Commander-bao/BlueberryPi/2.Docs/Allwinner H6/硬件资料/9、原型机设计资料/H6_PRO_DDR3_V1_1.pdf

D | D
C | C
B | B
A | A
Schematics Index： | HJ
Revision | Description | Date | Drawn | Checked

# P01: REVISION HISTORY P02: BLOCK P03: POWER TREE P04: GPIO ASSIGNMENT P05: SOC1 P06: SOC2 P07: DDR3 16X2 P08: POWER P09: NAND-eMMC P10: CARD-USB-IR-SPDIF P11: KEY-LED-ETH-DEBUG P12: AV-HDMI P13: WIFI-BT 2T2R P14: WIFI-BT 1T1R

Ver 0.5 | Initial Version | 2016-12-26

# REVISION HISTORY

Ver 0.9 | 2017-04-10 | HJ
Ver 1.0 | 2017-06-14 | HJ

Design Name

Size A3 | Page Name REVISION HISTORY REVISION HISTORY REVISION HISTORY | Rev
Date: Thursday, June 22, 2017 Thursday, June 22, 2017 Thursday, June 22, 2017 | Sheet 1 1 1 of 14 14 14

# AllWinner Technology Co.,Ltd

## H6-PROTO

Design Name

# AllWinner Technology Co.,Ltd

Design Name

# AllWinner Technology Co.,Ltd

# confidential

D | D

# BLOCK

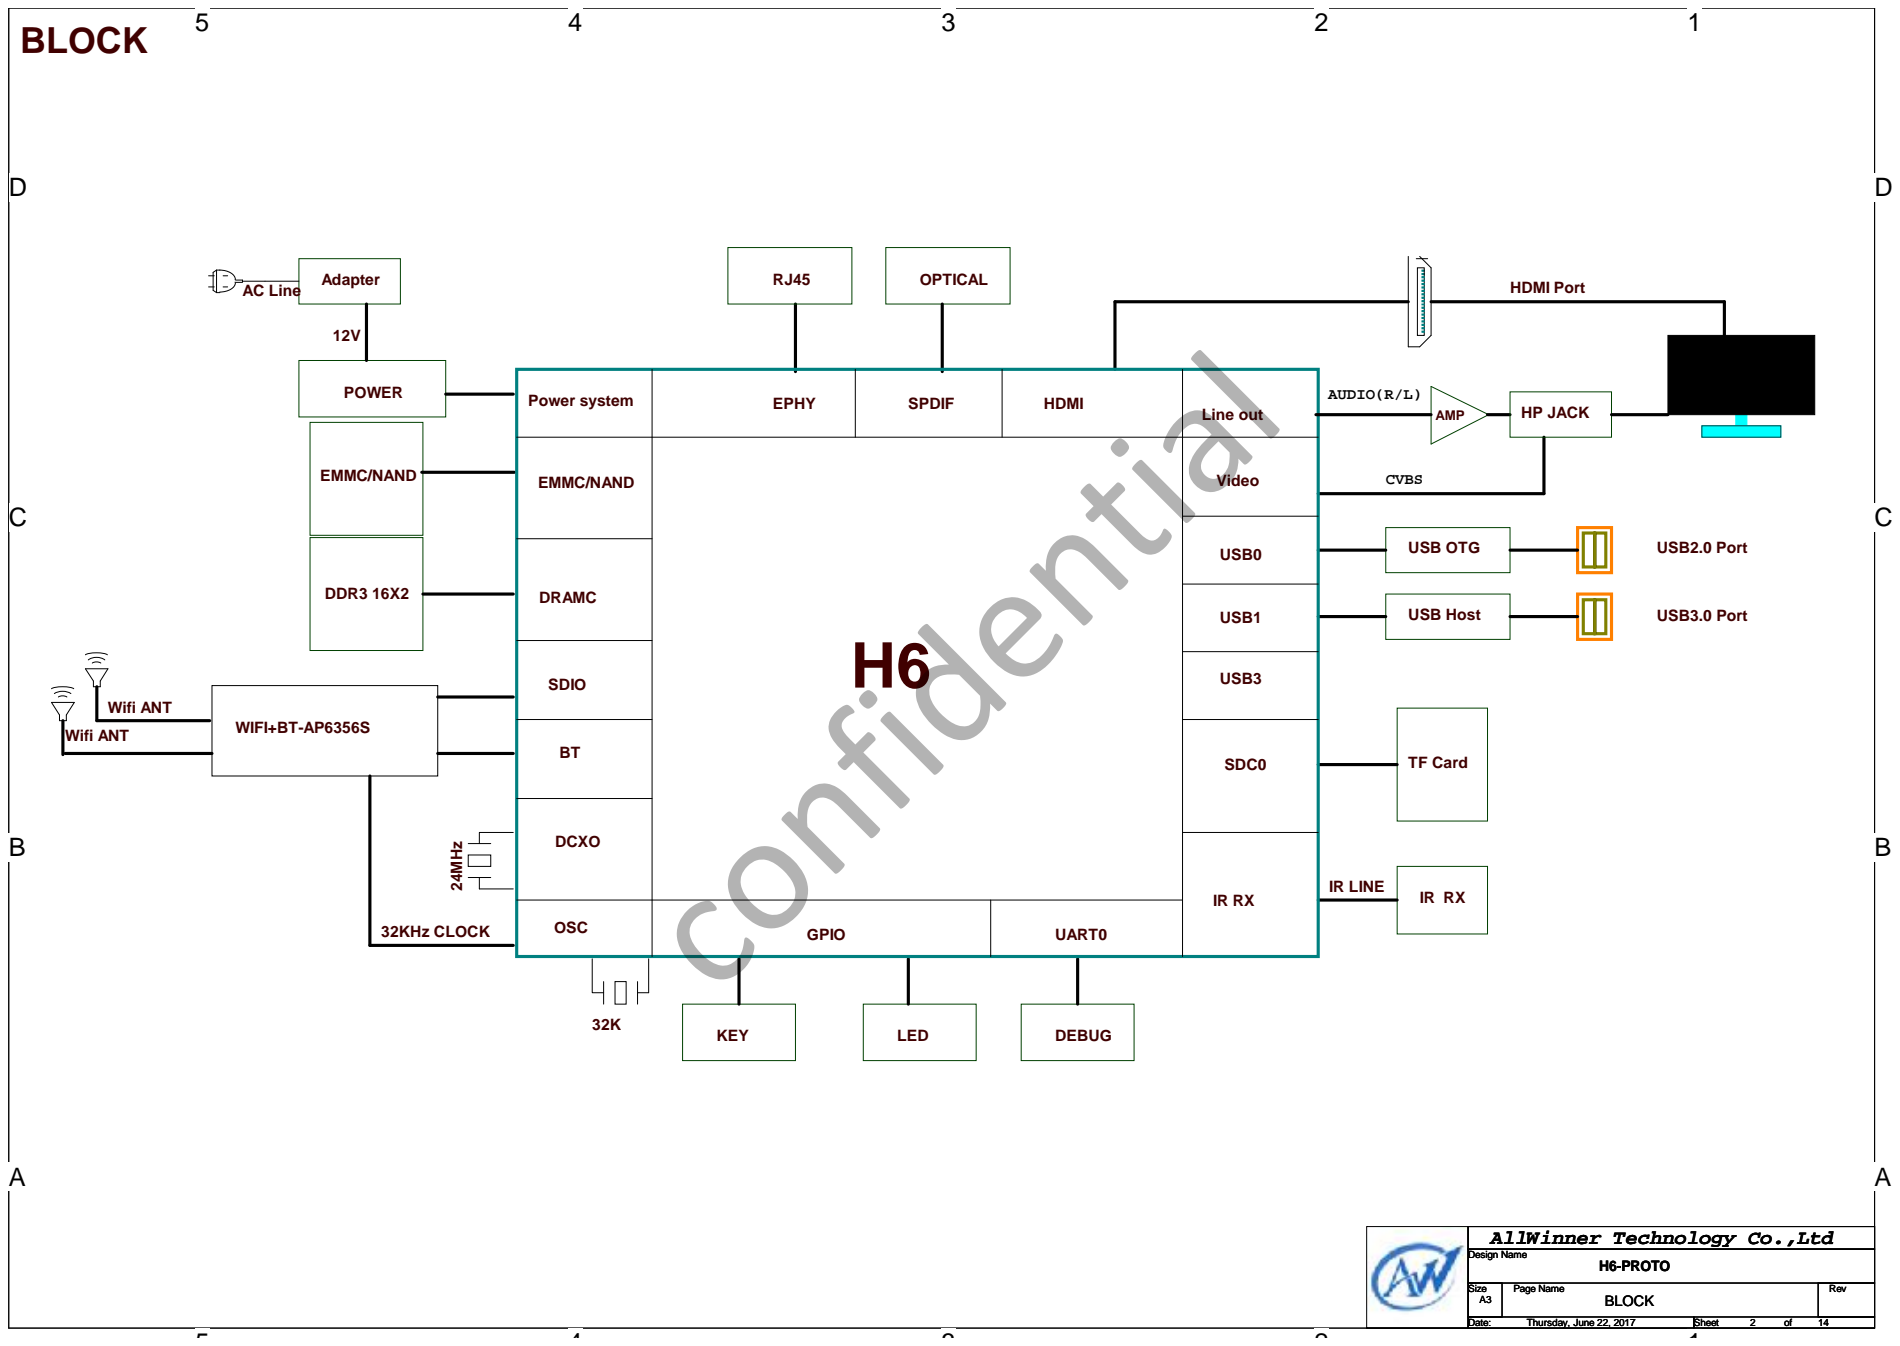
[picture p25: page 2]
UART0; KEY; DEBUG; GPIO; Power system; EMMC/NAND; EPHY; SPDIF; HDMI; OSC; USB1; USB2.0 Port; USB3.0 Port; USB OTG; WIFI+BT-AP6356S; Wifi ANT; LED; SDC0; TF Card; IR LINE; USB0; Video; Line out; AUDIO(R/L); AMP; CVBS; HP JACK; HDMI Port Adapter; OPTICAL; POWER; AC Line; DRAMC; DDR3 16X2; SDIO; USB3; USB Host; DCXO; 24MHz; 32KHz CLOCK; Design Name; BLOCK; Thursday, June 22, 2017; confidential

AllWinner Technology Co.,Ltd

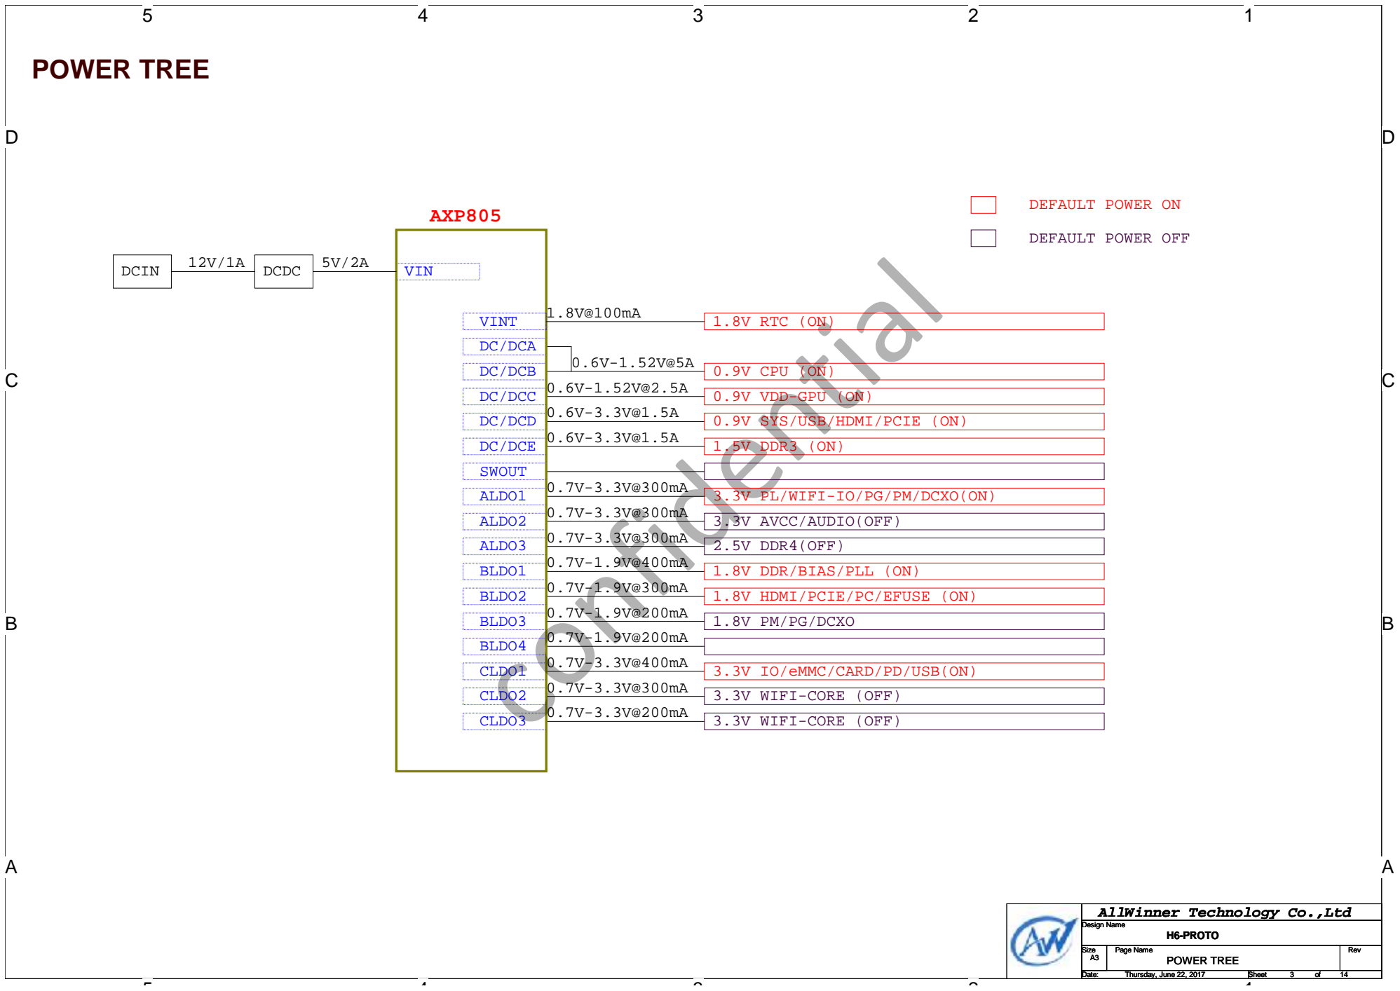
[picture p26: figure]
POWER TREE; 3.3V WIFI-CORE (OFF); 0.9V VDD-GPU (ON) 0.6V-1.52V@2.5A; DC/DCA DC/DCB; VIN; DC/DCC; 0.9V CPU (ON); DC/DCD 1.5V DDR3 (ON) 0.6V-3.3V@1.5A DC/DCE; SWOUT; ALDO1; 3.3V PL/WIFI-IO/PG/PM/DCXO(ON); ALDO2; ALDO3; 1.8V DDR/BIAS/PLL (ON); BLDO2 0.7V-1.9V@200mA BLDO3; CLDO1; BLDO4; CLDO2 CLDO3; AXP805; 2.5V DDR4(OFF); 1.8V PM/PG/DCXO; 3.3V AVCC/AUDIO(OFF); 1.8V HDMI/PCIE/PC/EFUSE (ON); 3.3V IO/eMMC/CARD/PD/USB(ON); BLDO1; DCIN; 0.9V SYS/USB/HDMI/PCIE (ON); VINT; 1.8V RTC (ON) 1.8V@100mA; DEFAULT POWER ON; DEFAULT POWER OFF; DCDC; Design Name; AllWinner Technology Co.,Ltd; POWER TREE POWER TREE POWER TREE; confidential

Thursday, June 22, 2017 Thursday, June 22, 2017 Thursday, June 22, 2017 | 3 3 3 14 14 14

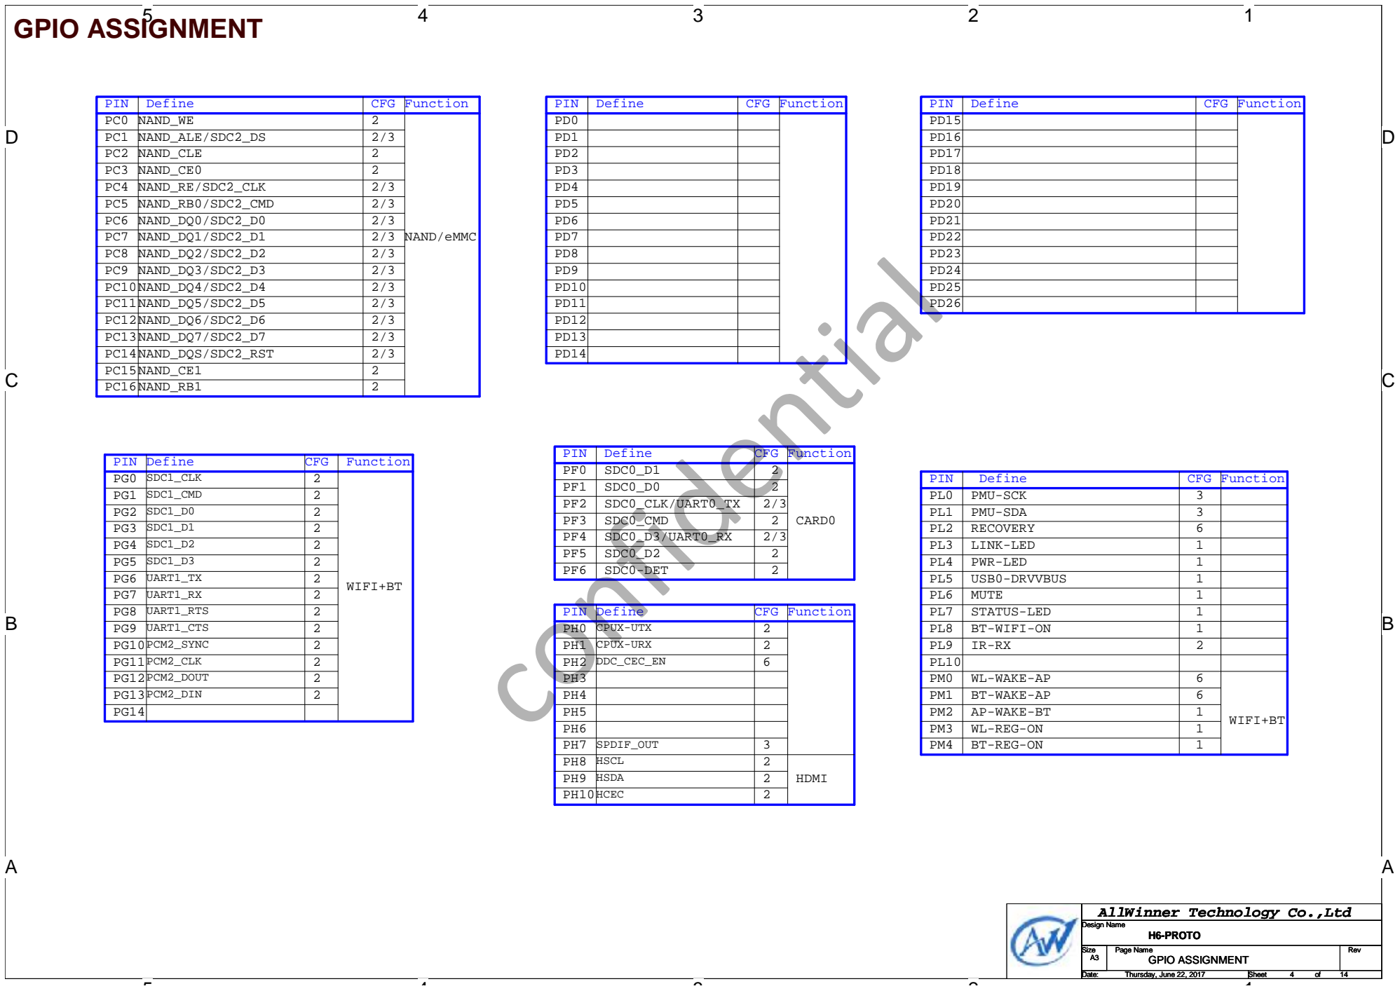
[picture p27: figure]
GPIO ASSIGNMENT; SDC0_D2; SDC0_CMD; SDC0_CLK/UART0_TX; SDC0_D1 SDC0_D0; SDC0_D3/UART0_RX; CARD0 SDC1_D1; SDC1_D0; SDC1_CMD; SDC1_CLK; UART1_RTS; UART1_RX; UART1_TX; SDC1_D3; SDC1_D2; SDC0-DET; PIN; Define; CFG; Function; NAND_DQ4/SDC2_D4; NAND_DQ3/SDC2_D3; NAND_DQ7/SDC2_D7; NAND_DQ6/SDC2_D6; NAND_DQ5/SDC2_D5; NAND_CE1; NAND_DQS/SDC2_RST; NAND_DQ1/SDC2_D1 NAND_DQ2/SDC2_D2; NAND_DQ0/SDC2_D0; NAND_RB0/SDC2_CMD; NAND_ALE/SDC2_DS NAND_CLE; NAND_WE; NAND_CE0 NAND_RE/SDC2_CLK; NAND_RB1; NAND/eMMC; PCM2_DIN; PCM2_DOUT; PCM2_CLK; PCM2_SYNC; UART1_CTS; SPDIF_OUT; HCEC; HSDA; PMU-SCK; PWR-LED; LINK-LED; RECOVERY; PMU-SDA; STATUS-LED; MUTE; WL-REG-ON; AP-WAKE-BT; BT-WAKE-AP; WL-WAKE-AP; BT-REG-ON; CPUX-UTX CPUX-URX; WIFI+BT; USB0-DRVVBUS; BT-WIFI-ON; DDC_CEC_EN; Thursday, June 22, 2017; confidential

PH8 | HSCL | 2 | HDMI | AllWinner Technology Co.,Ltd AllWinner Technology Co.,Ltd AllWinner Technology Co.,Ltd Design Name Design Name Design Name GPIO ASSIGNMENT GPIO ASSIGNMENT GPIO ASSIGNMENT

D | D

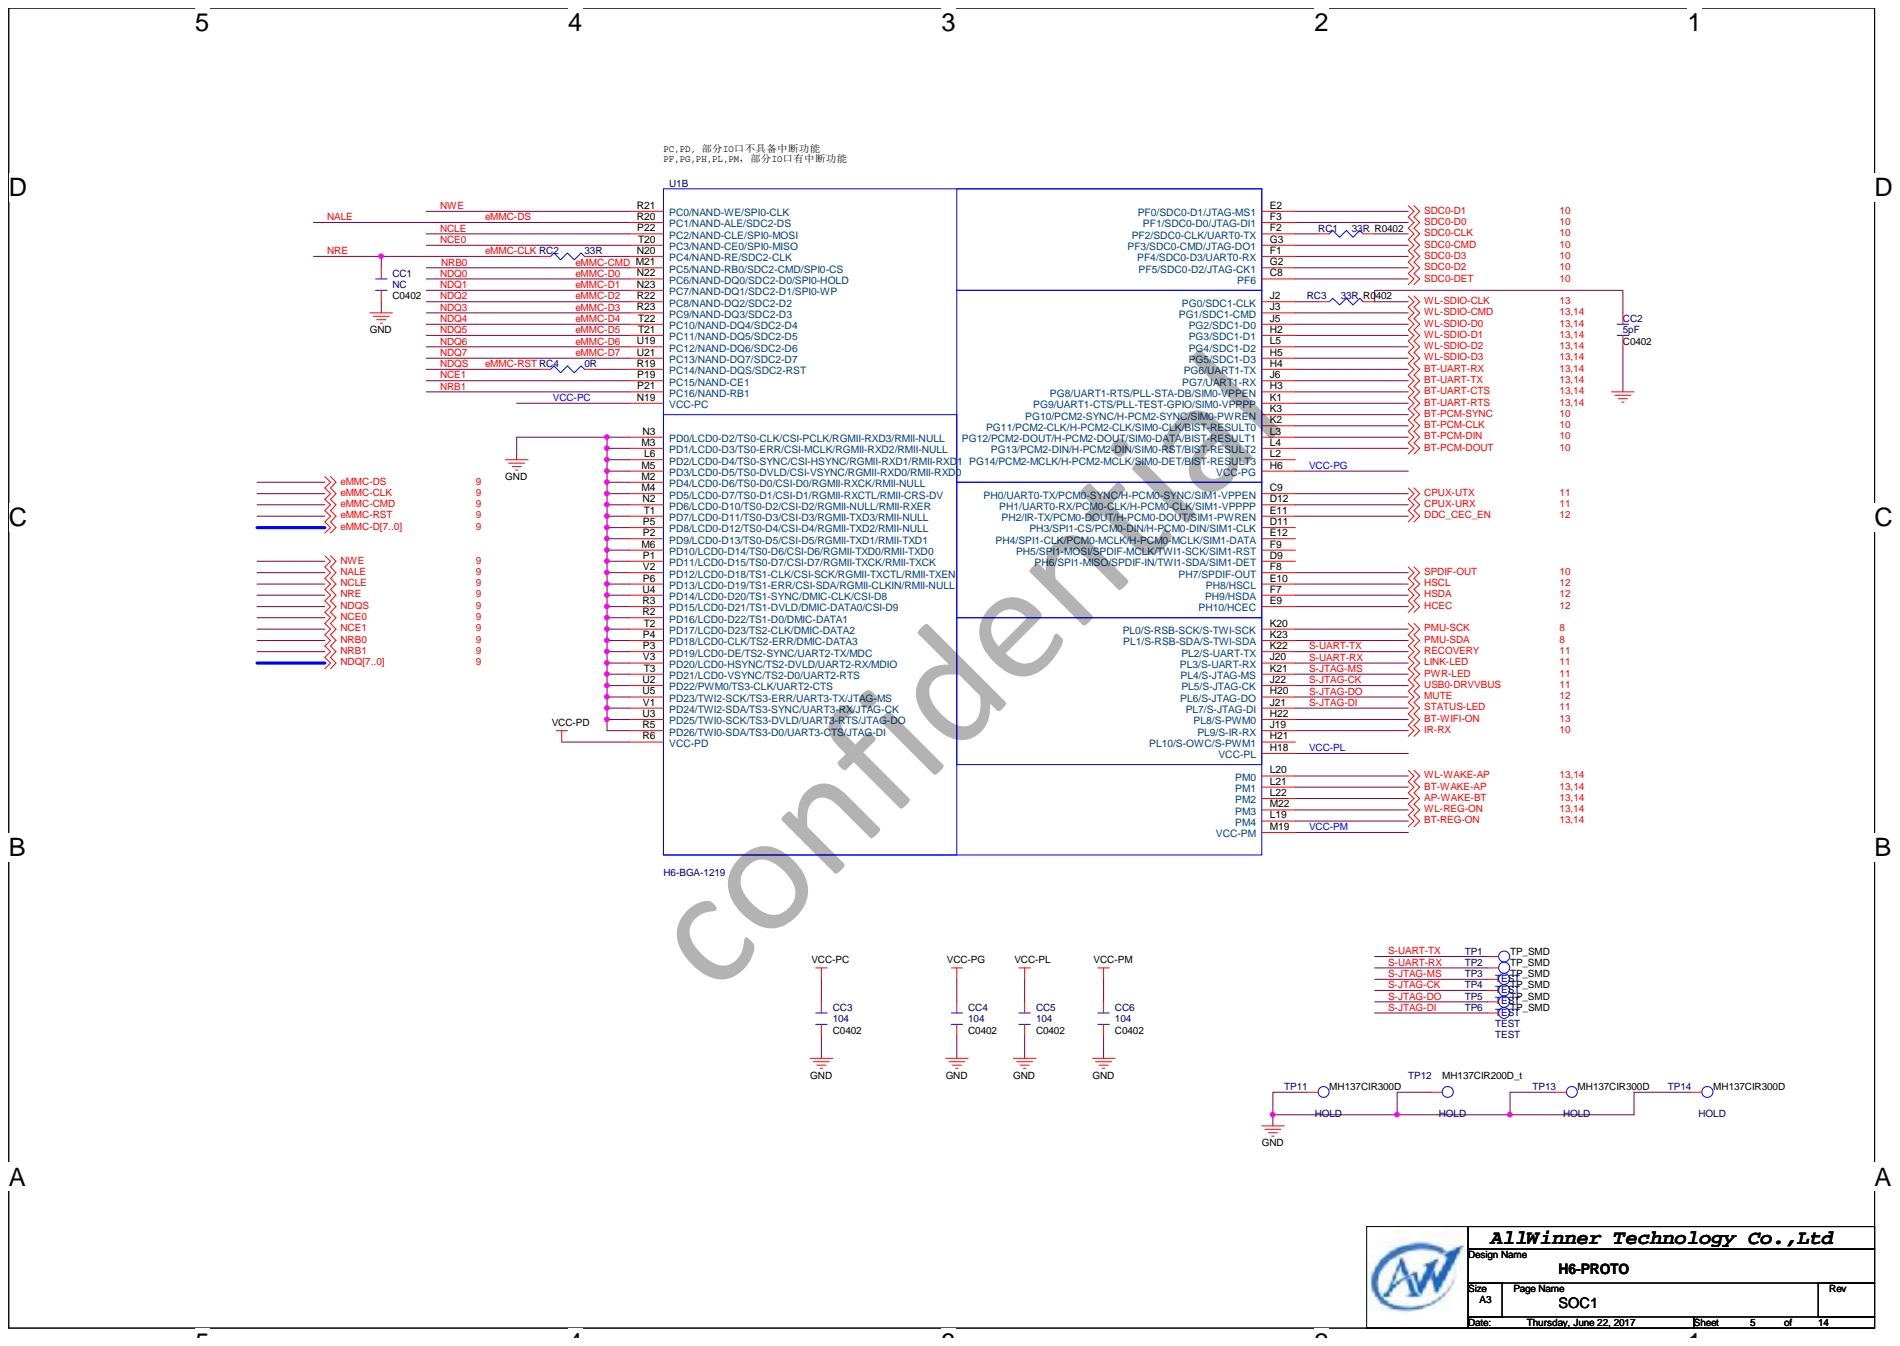
[picture p28: page 5]

PC,PD, 部分IO口不具备中断功能
PF,PG,PH,PL,PM，部分IO口有中断功能

PG8/UART1-RTS/PLL-STA-DB/SIM0-VPPEN
PG9/UART1-CTS/PLL-TEST-GPIO/SIM0-VPPPP
PG10/PCM2-SYNC/H-PCM2-SYNC/SIM0-PWREN

PD0/LCD0-D2/TS0-CLK/CSI-PCLK/RGMII-RXD3/RMII-NULL
PD1/LCD0-D3/TS0-ERR/CSI-MCLK/RGMII-RXD2/RMII-NULL
PD2/LCD0-D4/TS0-SYNC/CSI-HSYNC/RGMII-RXD1/RMII-RXD1
PD3/LCD0-D5/TS0-DVLD/CSI-VSYNC/RGMII-RXD0/RMII-RXD0
PD4/LCD0-D6/TS0-D0/CSI-D0/RGMII-RXCK/RMII-NULL
PD5/LCD0-D7/TS0-D1/CSI-D1/RGMII-RXCTL/RMII-CRS-DV M4
PD6/LCD0-D10/TS0-D2/CSI-D2/RGMII-NULL/RMII-RXER
PD7/LCD0-D11/TS0-D3/CSI-D3/RGMII-TXD3/RMII-NULL
PD8/LCD0-D12/TS0-D4/CSI-D4/RGMII-TXD2/RMII-NULL
PD9/LCD0-D13/TS0-D5/CSI-D5/RGMII-TXD1/RMII-TXD1
PD10/LCD0-D14/TS0-D6/CSI-D6/RGMII-TXD0/RMII-TXD0
PD11/LCD0-D15/TS0-D7/CSI-D7/RGMII-TXCK/RMII-TXCK P1
PD12/LCD0-D18/TS1-CLK/CSI-SCK/RGMII-TXCTL/RMII-TXEN
PD13/LCD0-D19/TS1-ERR/CSI-SDA/RGMII-CLKIN/RMII-NULL
PD14/LCD0-D20/TS1-SYNC/DMIC-CLK/CSI-D8
PD15/LCD0-D21/TS1-DVLD/DMIC-DATA0/CSI-D9
PD16/LCD0-D22/TS1-D0/DMIC-DATA1
PD17/LCD0-D23/TS2-CLK/DMIC-DATA2
PD18/LCD0-CLK/TS2-ERR/DMIC-DATA3
PD19/LCD0-DE/TS2-SYNC/UART2-TX/MDC P3
PD20/LCD0-HSYNC/TS2-DVLD/UART2-RX/MDIO V3
PD21/LCD0-VSYNC/TS2-D0/UART2-RTS T3
PD22/PWM0/TS3-CLK/UART2-CTS U2
PD23/TWI2-SCK/TS3-ERR/UART3-TX/JTAG-MS U5
PD24/TWI2-SDA/TS3-SYNC/UART3-RX/JTAG-CK V1
PD25/TWI0-SCK/TS3-DVLD/UART3-RTS/JTAG-DO U3
PD26/TWI0-SDA/TS3-D0/UART3-CTS/JTAG-DI R5
VCC-PD R6

PG11/PCM2-CLK/H-PCM2-CLK/SIM0-CLK/BIST-RESULT0
PG12/PCM2-DOUT/H-PCM2-DOUT/SIM0-DATA/BIST-RESULT1
PG13/PCM2-DIN/H-PCM2-DIN/SIM0-RST/BIST-RESULT2
PG14/PCM2-MCLK/H-PCM2-MCLK/SIM0-DET/BIST-RESULT3

PH0/UART0-TX/PCM0-SYNC/H-PCM0-SYNC/SIM1-VPPEN
PH1/UART0-RX/PCM0-CLK/H-PCM0-CLK/SIM1-VPPPP
PH2/IR-TX/PCM0-DOUT/H-PCM0-DOUT/SIM1-PWREN
PH3/SPI1-CS/PCM0-DIN/H-PCM0-DIN/SIM1-CLK D11
PH4/SPI1-CLK/PCM0-MCLK/H-PCM0-MCLK/SIM1-DATA
PH5/SPI1-MOSI/SPDIF-MCLK/TWI1-SCK/SIM1-RST F9
PH6/SPI1-MISO/SPDIF-IN/TWI1-SDA/SIM1-DET

PL0/S-RSB-SCK/S-TWI-SCK K20
PL1/S-RSB-SDA/S-TWI-SDA K23

AllWinner Technology Co.,Ltd

D | D

## TEST

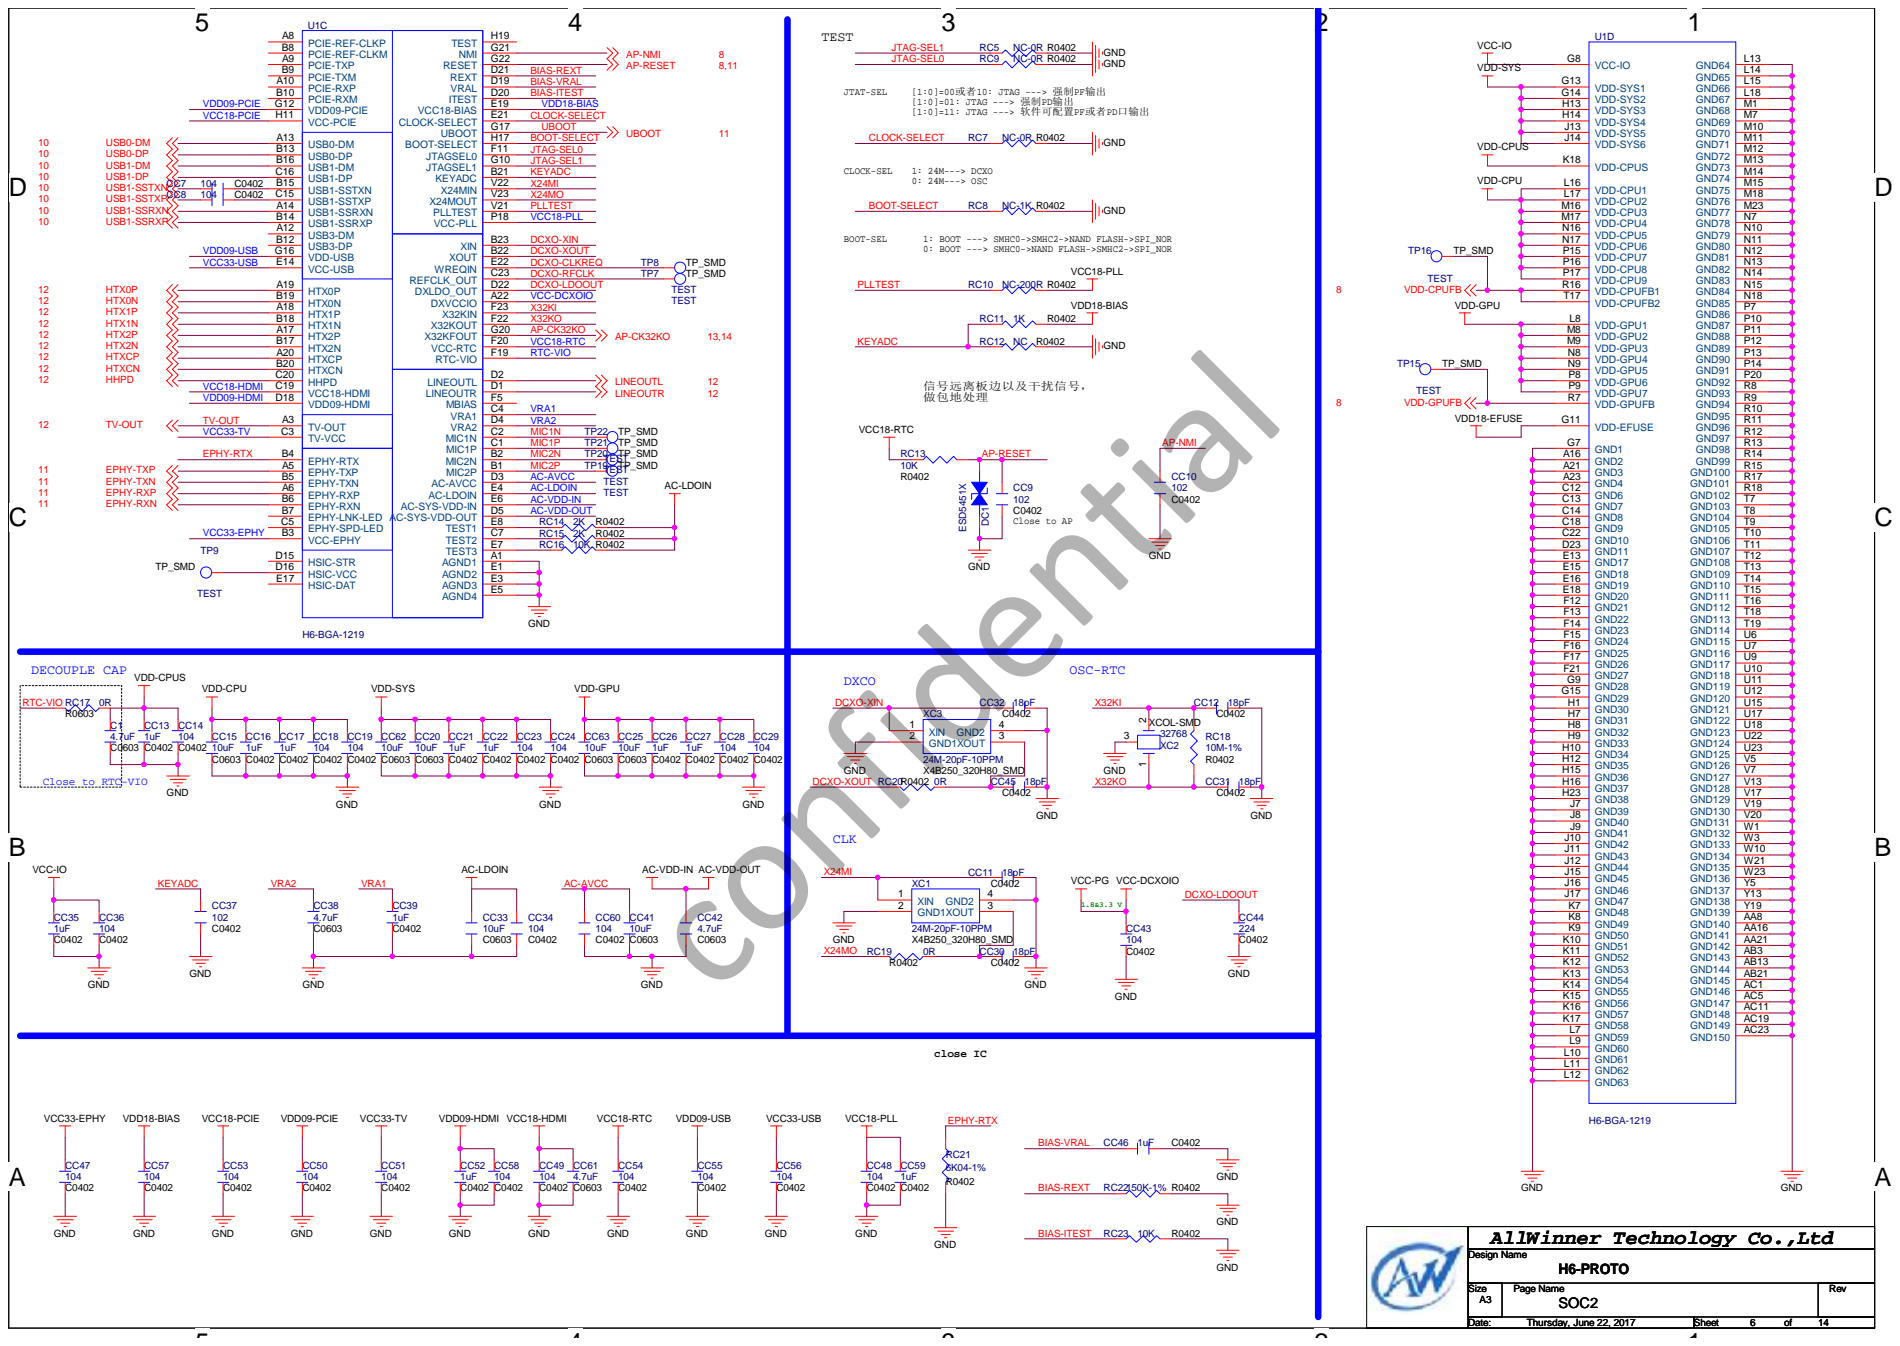
[picture p29: page 6]

VCC-EPHY B3
E17 HSIC-VCC D16 HSIC-STR

Close to RTC-VIO

VCC-PG VCC-DCXOIO

AllWinner Technology Co.,Ltd

D

D

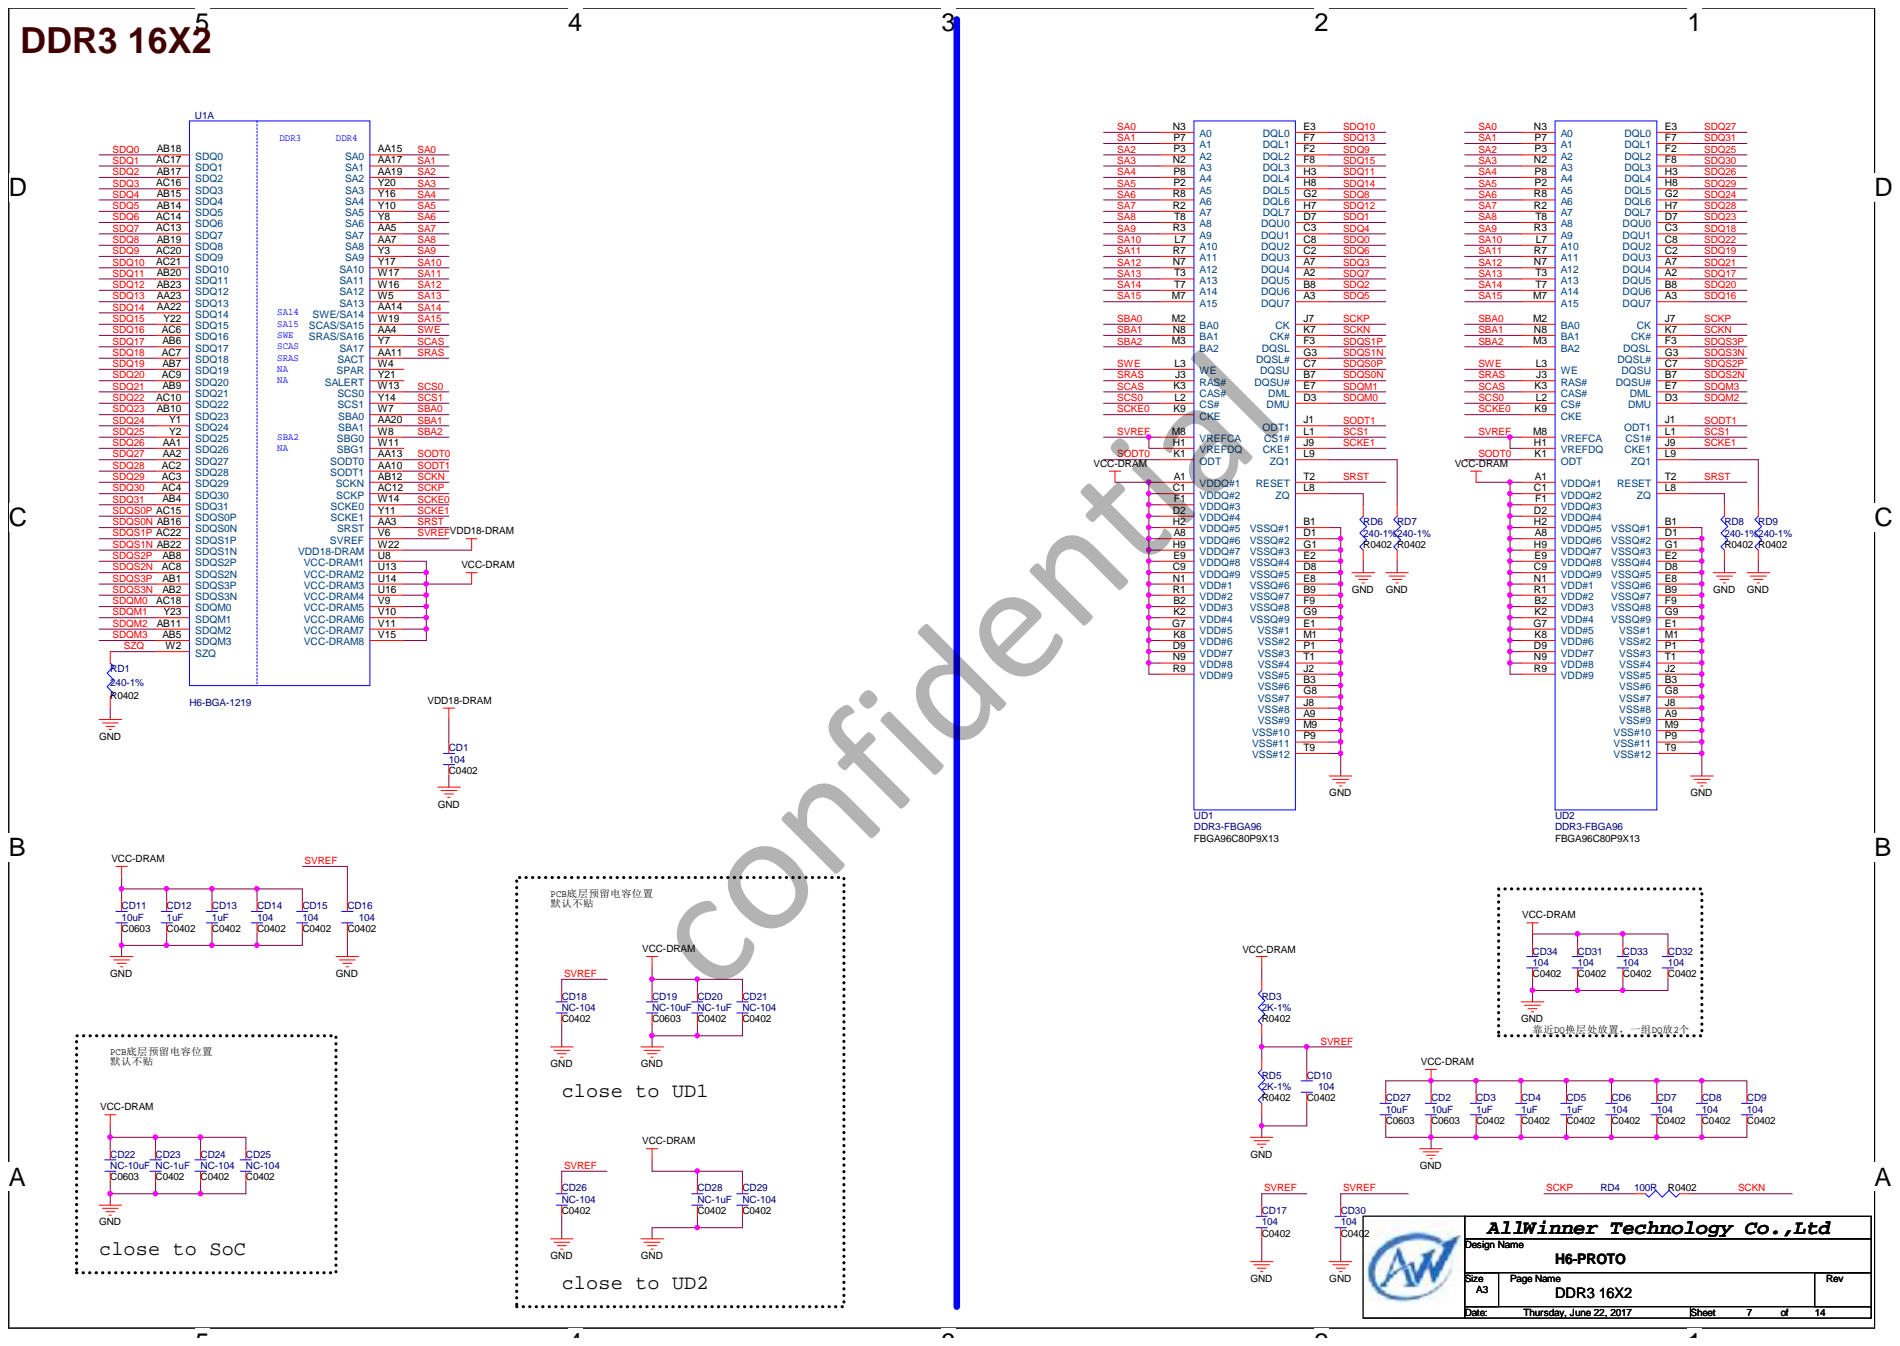
[picture p30: page 7]

SCKP
AllWinner Technology Co.,Ltd

# DCIN

12V->5V

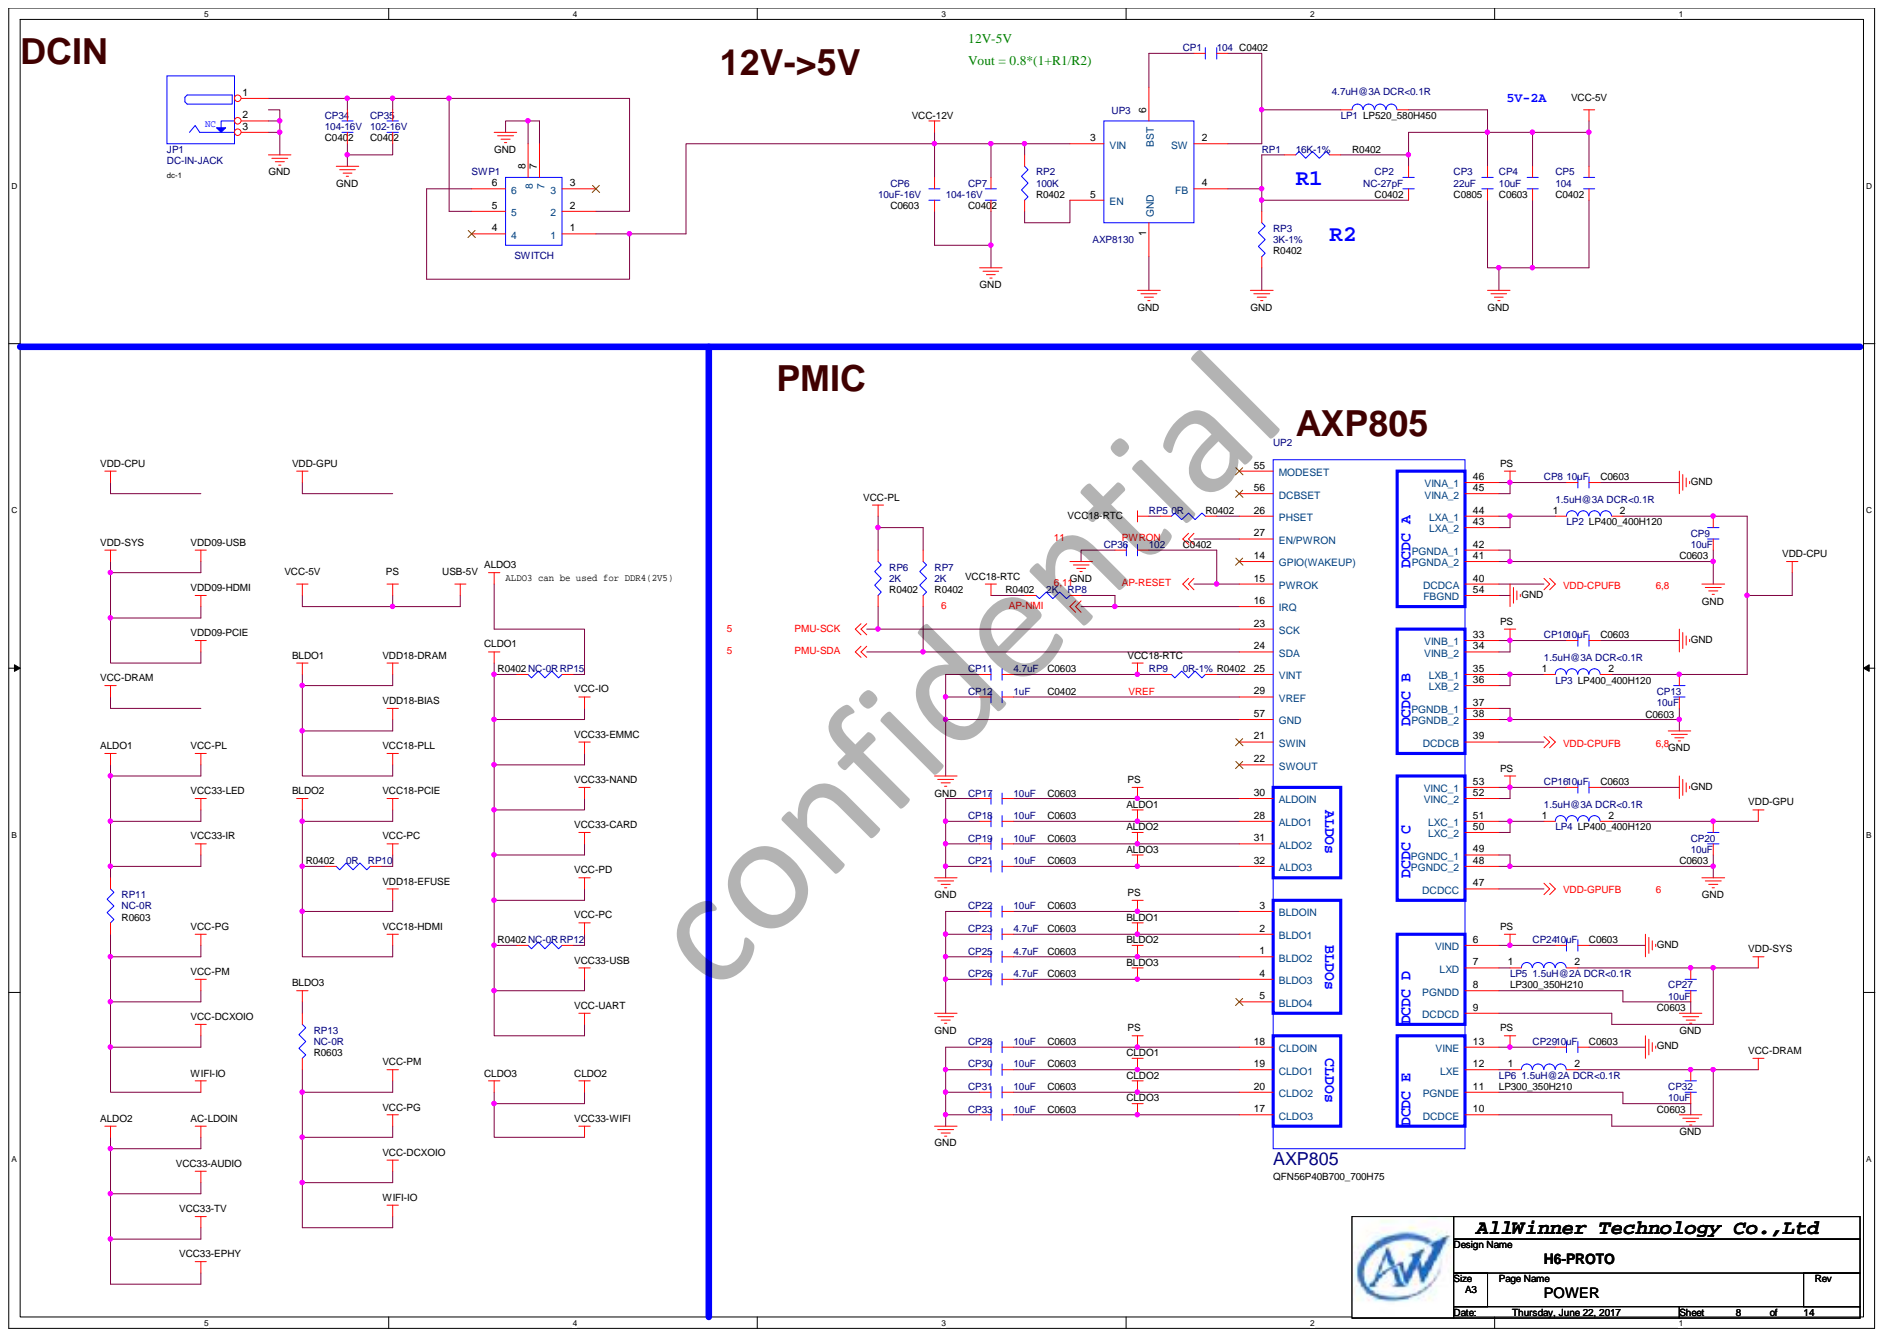
[picture p31: page 8]

ALDO3
ALDO3 can be used for DDR4(2V5)

AllWinner Technology Co.,Ltd

D | D

# NAND eMMC

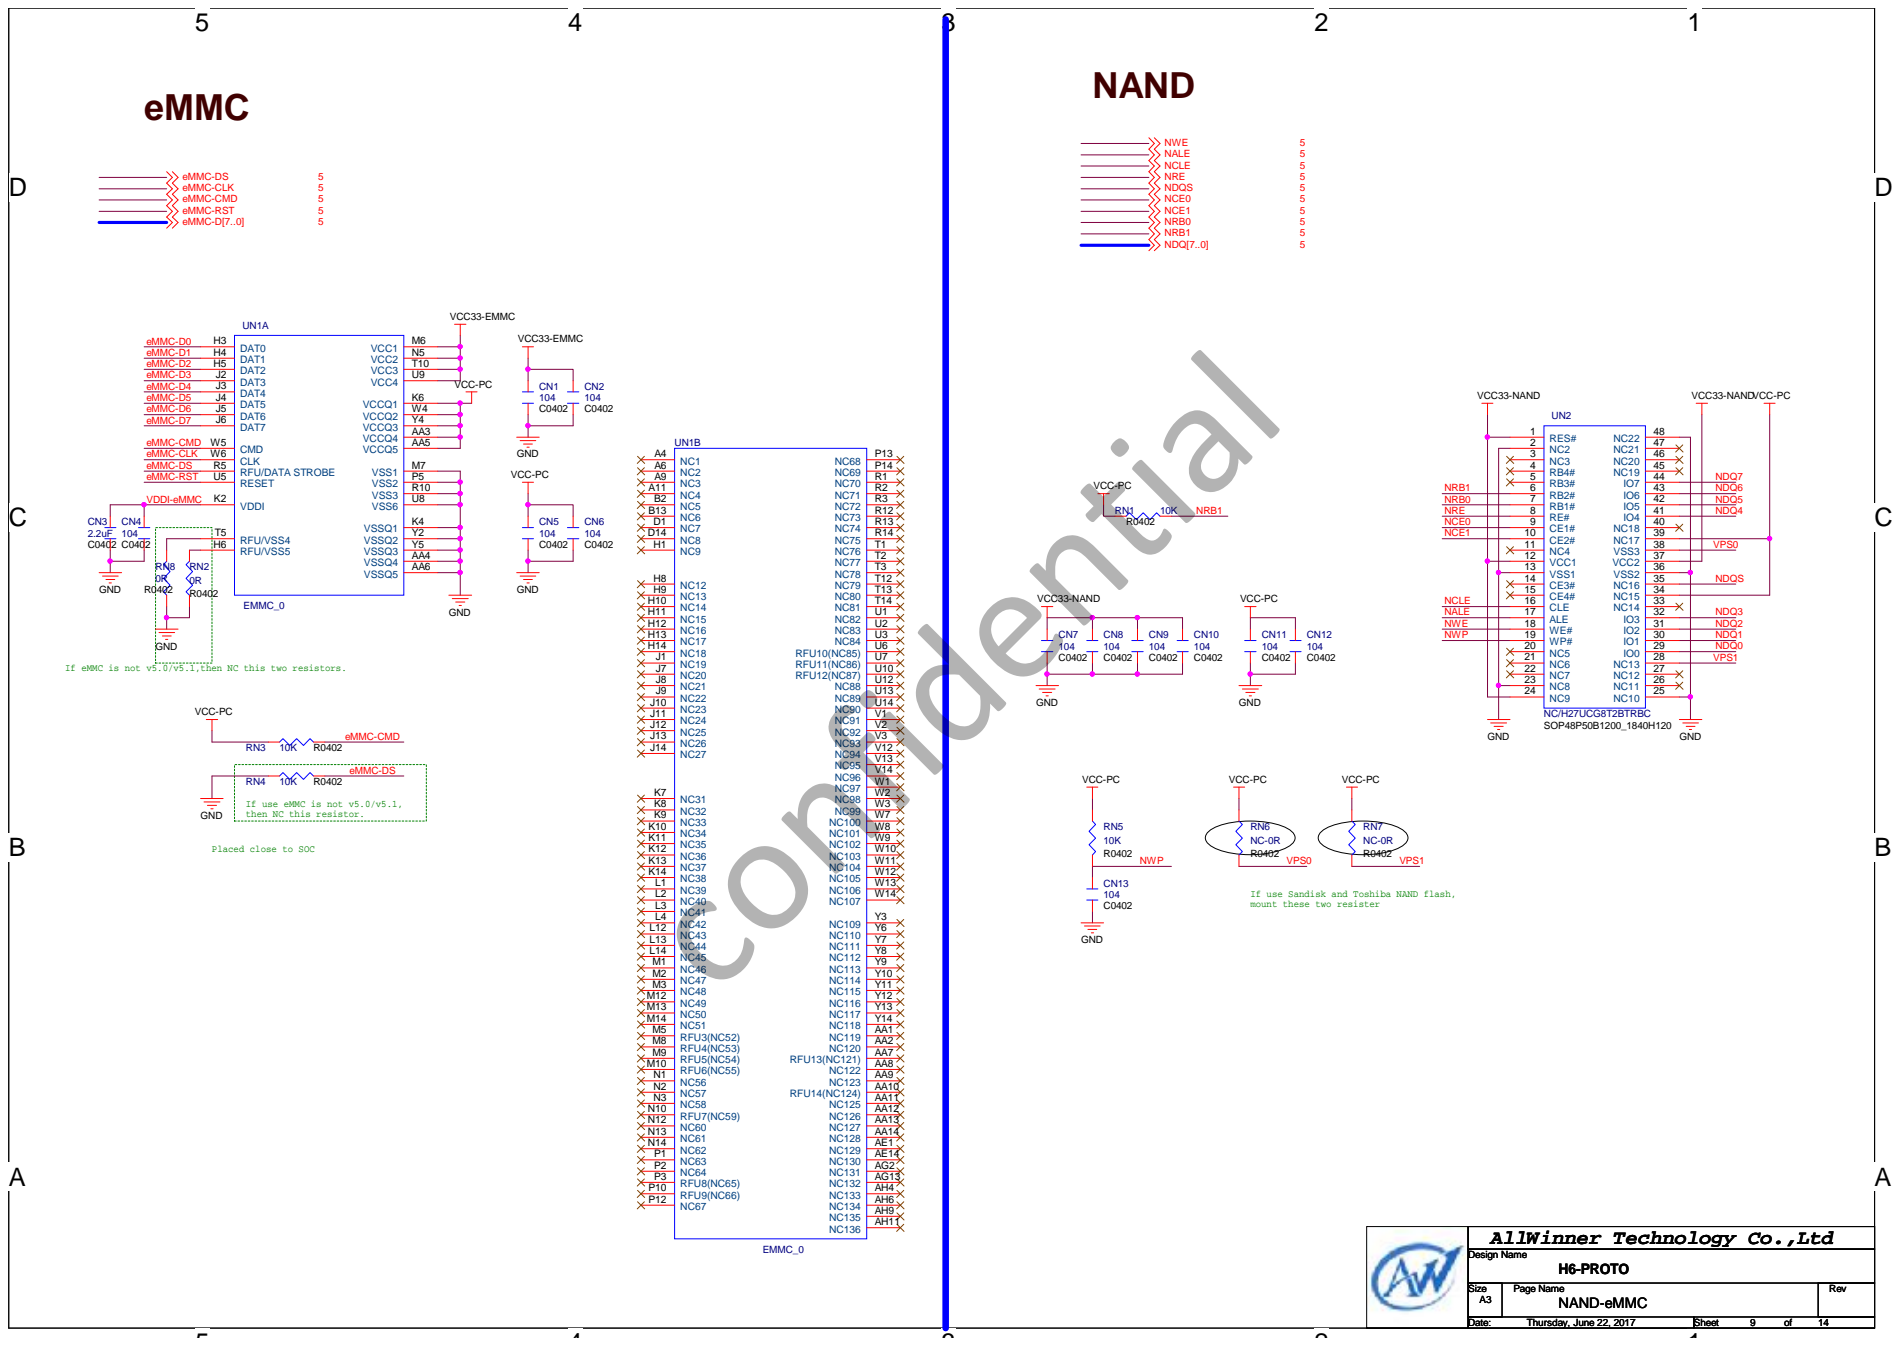
[picture p32: page 9]

If eMMC is not v5.0/v5.1,then NC this two resistors.

If use eMMC is not v5.0/v5.1,
then NC this resistor.

Placed close to SOC

If use Sandisk and Toshiba NAND flash,
mount these two resister

AllWinner Technology Co.,Ltd

D

D

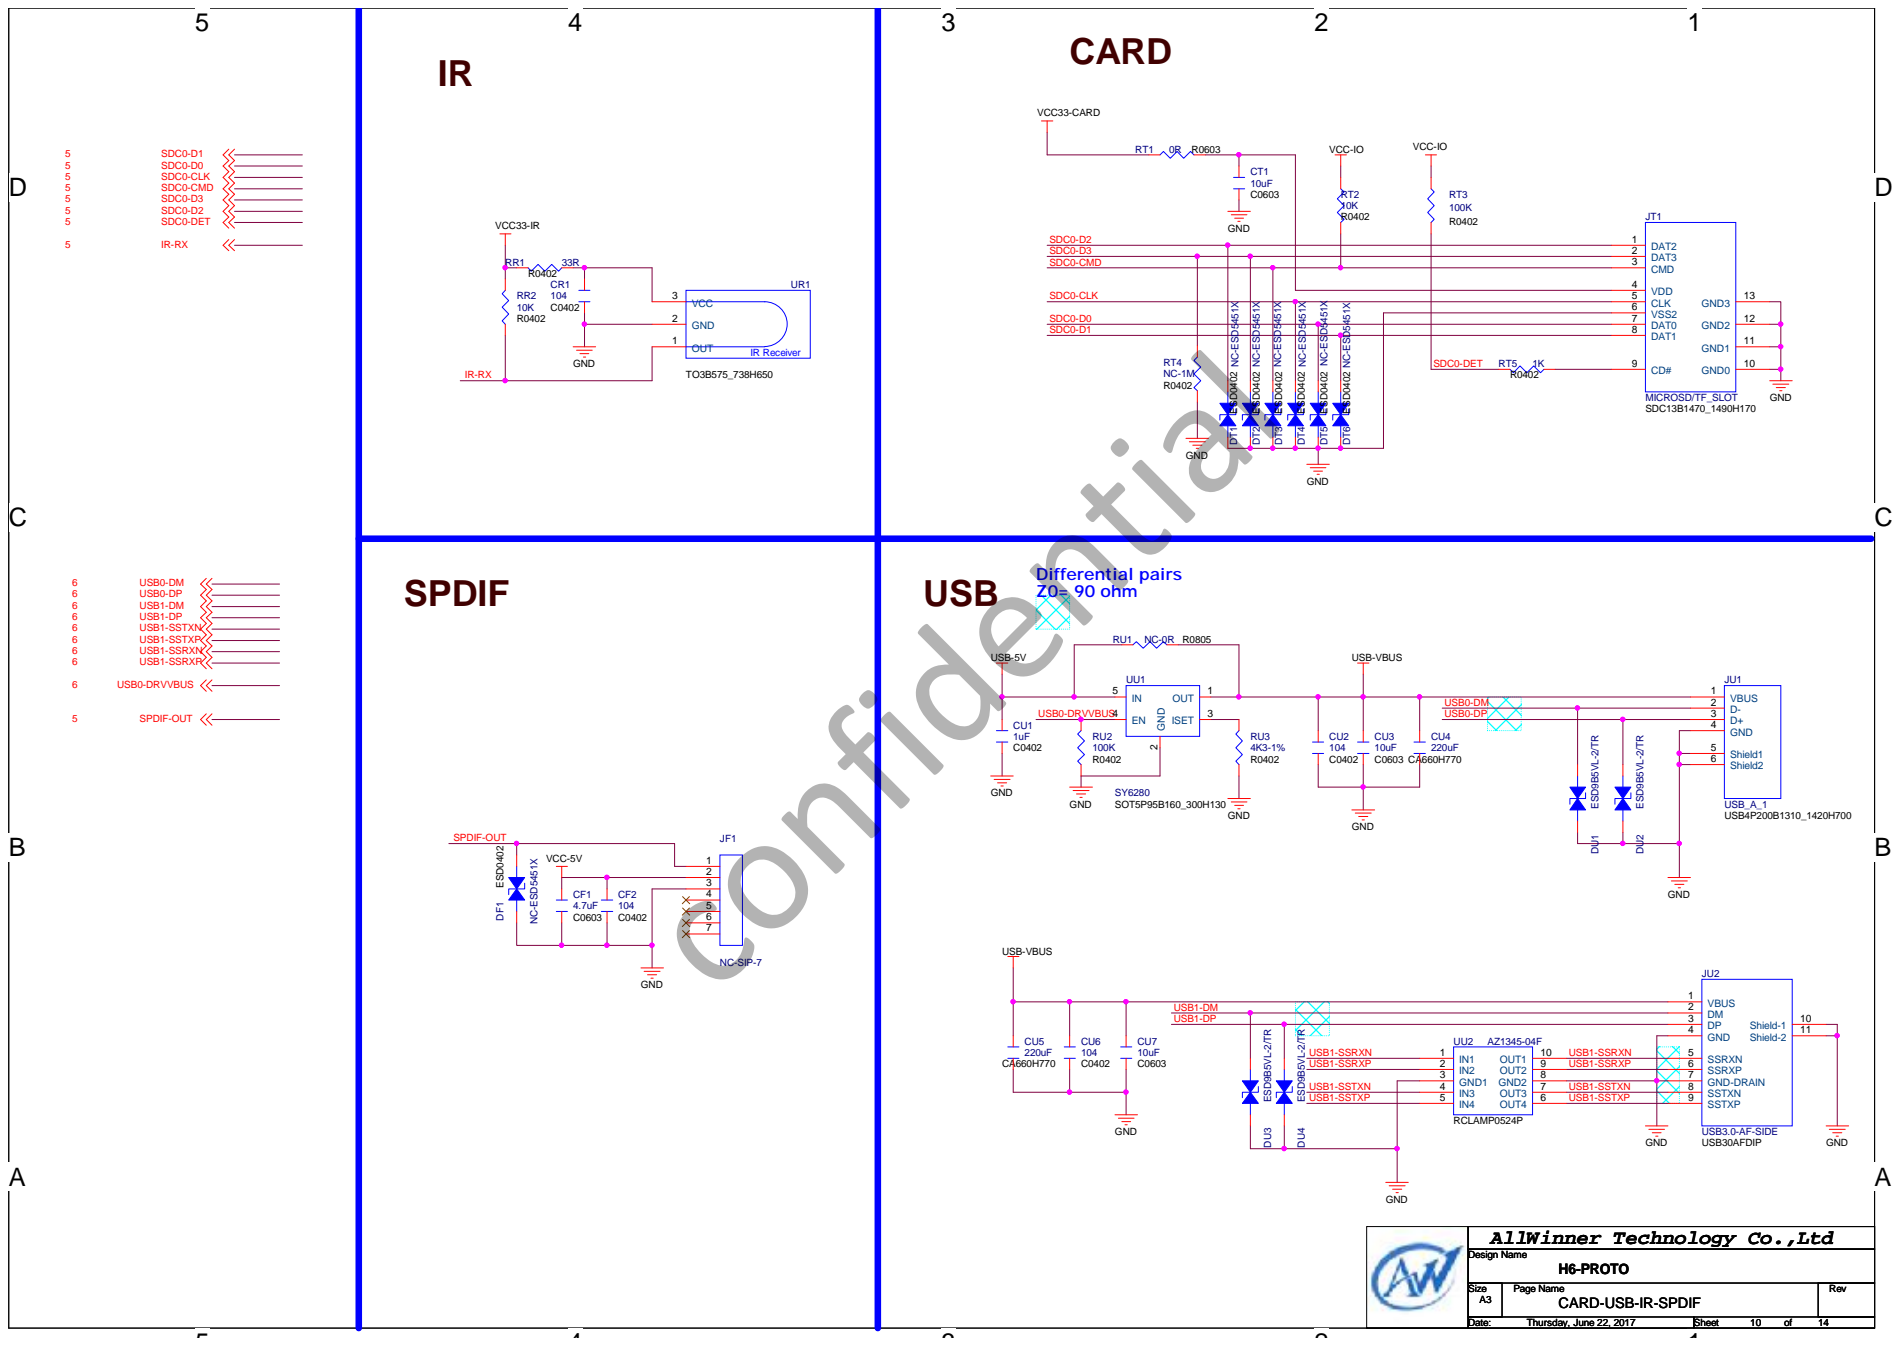
[picture p33: page 10]
USB; Diff; renti; al pairs; SPDIF; SDC; CLK; CMD; SDC0; -DET; -DRVVBUS; -SSRXN USB1; -SSRXP; USB1; -SSTXN USB1; -OUT; -SSTXP; -SSTXN; VCC; VCC33; -CARD; -VBUS; GND; -SSRXN; sign; ame; Size; Rev; ate:; Sheet; OTO; Thurs; Jun; DT4 NC-ESD5451X ESD0402; DU1 ESD9B5VL-2/TR; DT5 NC-ESD5451X ESD0402; JT1 MICROSD; /TF_SLOT; SDC13B1470_1490H170 DAT3; VDD; VSS2; DAT0; DAT1; DAT2; GND0 10; GND1 11; GND2 12; GND3 13; SIP-7; DT2 NC-ESD5451X ESD0402; NC-ESD5451X; ESD0402; DT3 NC-ESD5451X ESD0402; RCLA; GND1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

0= 90 ohm CARD IR

DU4 ESD9B5VL-2/TR IR Receiver

-SSTXP IR-RX

AllWinner Technology Co.,Ltd CARD-USB-IR-SPDIF

# EPHY-FE

# Differential pairs

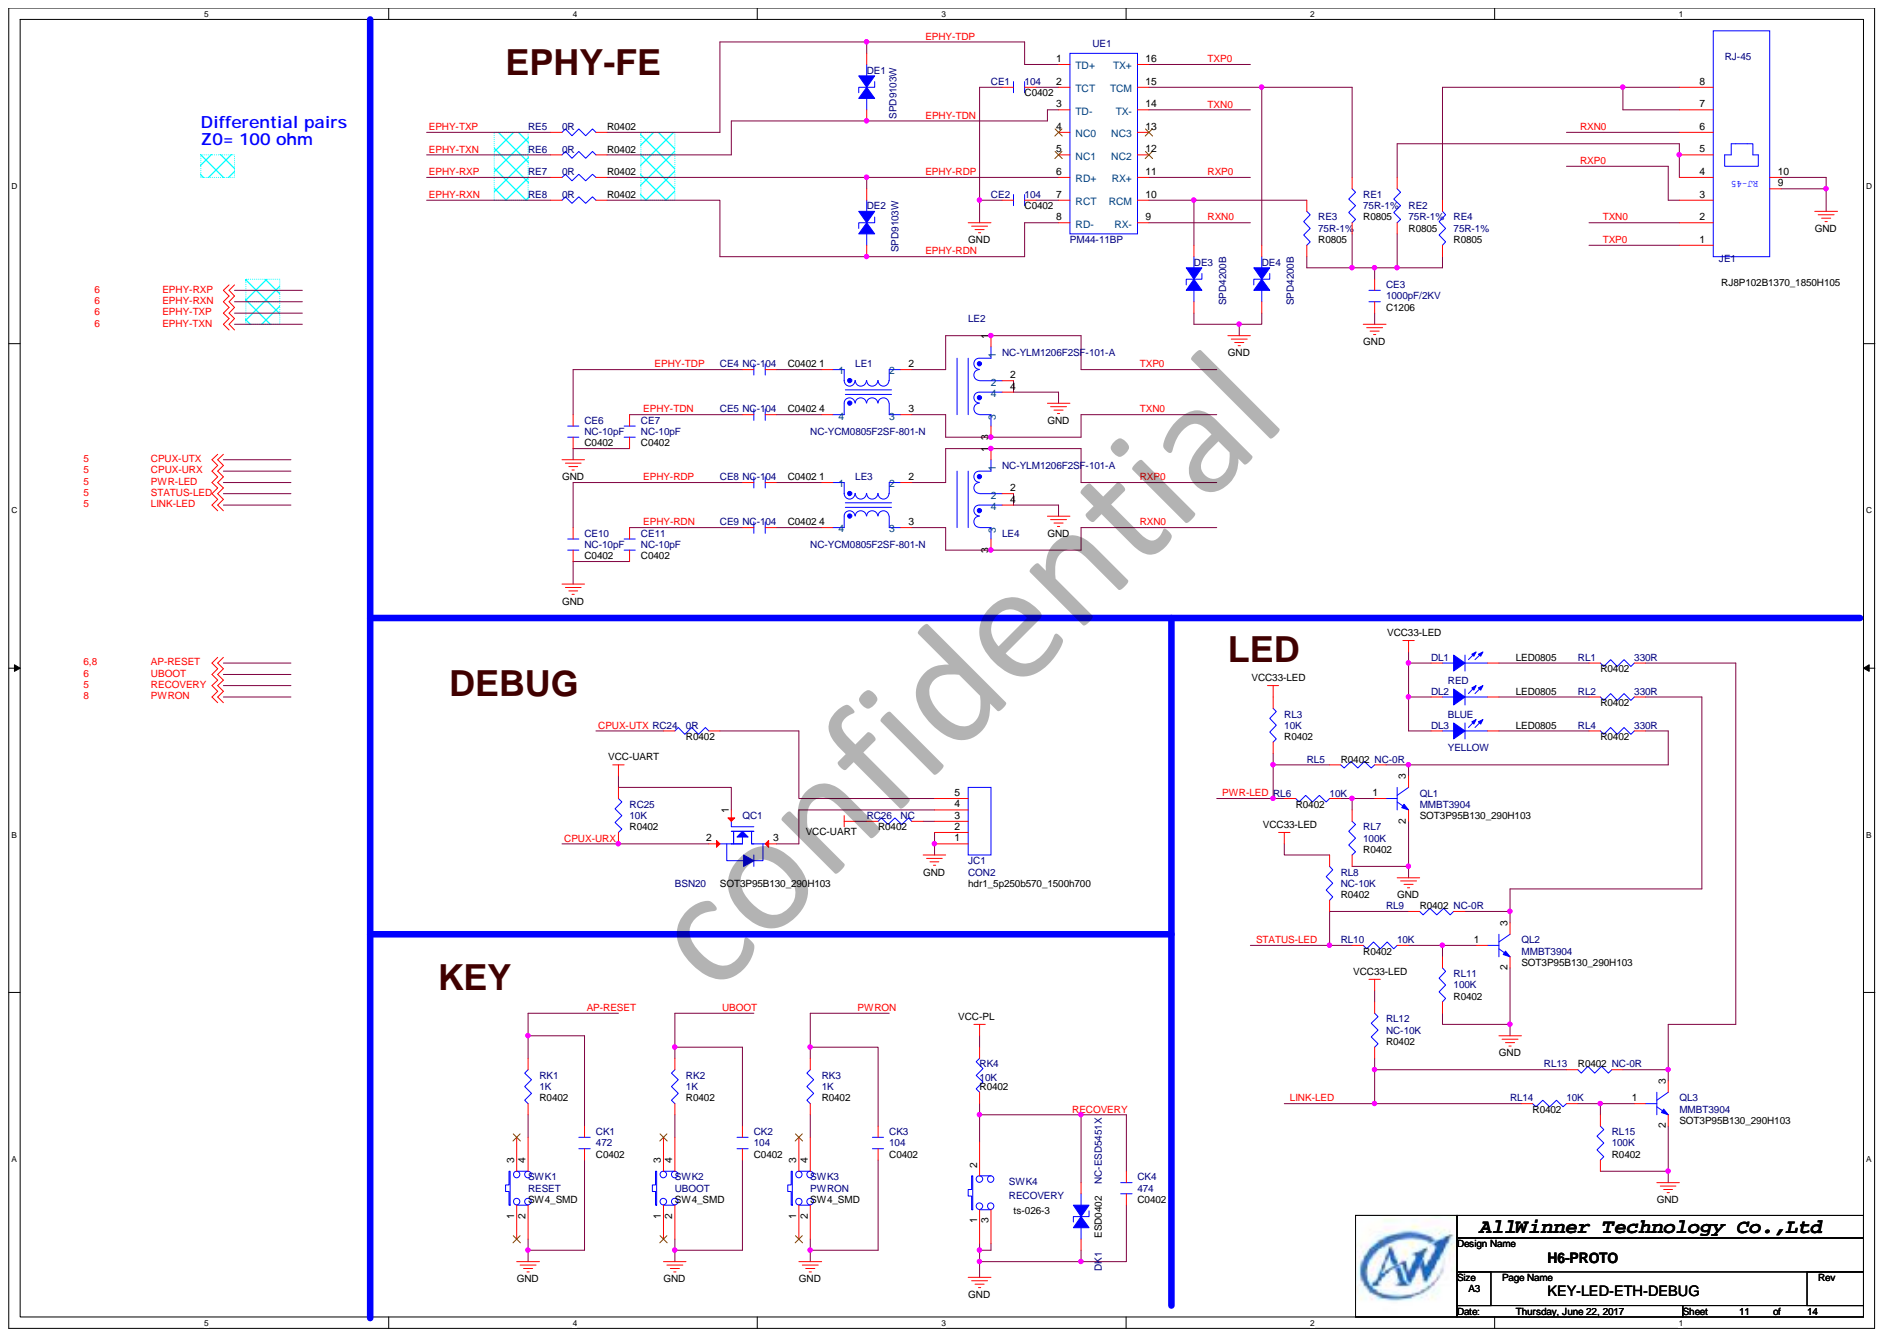
[picture p34: page 11]
DEBUG; Z0= 100 ohm; KEY; LED; CPUX-UTX; CPUX-URX; RECOVERY; PWR-LED; STATUS-LED; LINK-LED; AP-RESET; UBOOT; PWRON; RXN0; TXP0; TXN0; RXP0; EPHY-TDP; EPHY-TDN; EPHY-RDP; EPHY-RDN; EPHY-RXN; EPHY-RXP; EPHY-TXN; EPHY-TXP; VCC-UART; VCC-PL; VCC33-LED; GND; Design Name; H6-PROTO; Thursday, June 22, 2017; QL2 MMBT3904 SOT3P95B130_290H103; SPD9103W; SWK2 UBOOT SW4_SMD; SWK4 RECOVERY ts-026-3; NC-YLM1206F2SF-101-A; DK1 NC-ESD5451X ESD0402; NC-YCM0805F2SF-801-N; RED; LED0805; SPD4200B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

AllWinner Technology Co.,Ltd

KEY-LED-ETH-DEBUG

# A 输出2Vrms udio

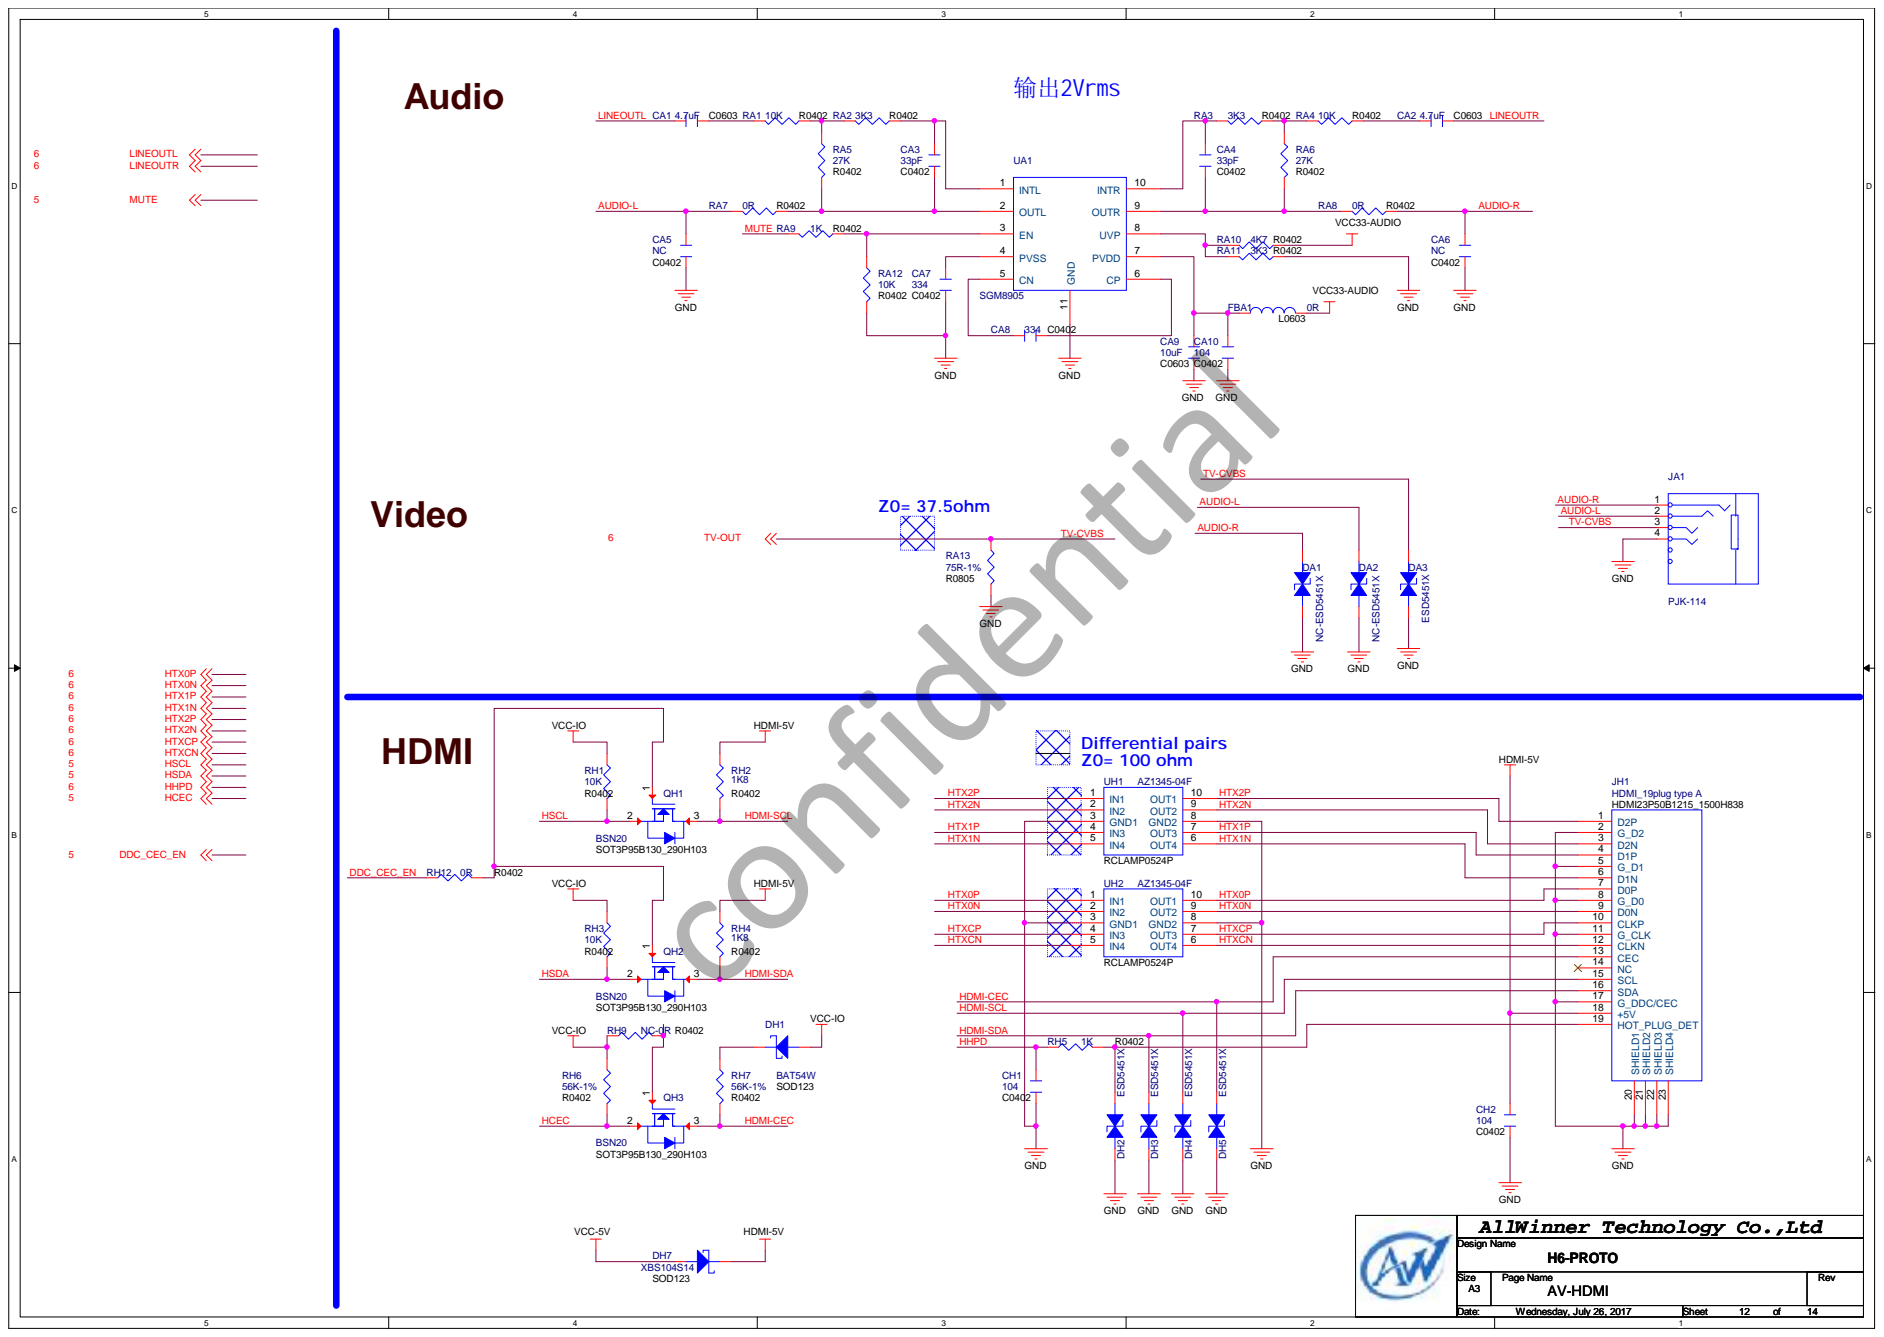
[picture p35: page 12]
Z0= 37.5ohm Video; Differential pairs HDMI; Z0= 100 ohm; LINEOUTL; TV-CVBS; HDMI-CEC; HTX2P; HTX0N; HTX1N; HTX1P; HTX2N; HTXCN; HTXCP; HTX2P HTX2N; HTX0P; HDMI-SDA; HDMI-SCL; HHPD; HSCL; AUDIO-L; AUDIO-R; AUDIO-L TV-CVBS; HSDA; HCEC; MUTE; LINEOUTR; DDC_CEC_EN; HDMI-5V; VCC-5V; VCC-IO; VCC33-AUDIO; GND; GND GND; TV-OUT; Design Name; AV-HDMI; H6-PROTO; Wednesday, July 26, 2017; BSN20 SOT3P95B130_290H103; PJK-114; RCLAMP0524P; GND1 3; OUT1; OUT2; 9 GND2 8; OUT3; OUT4; SGM8905; INTL; OUTL; PVSS 4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

GND GND

GND
AllWinner Technology Co.,Ltd

D | D

# WIFI+BT 2T2R

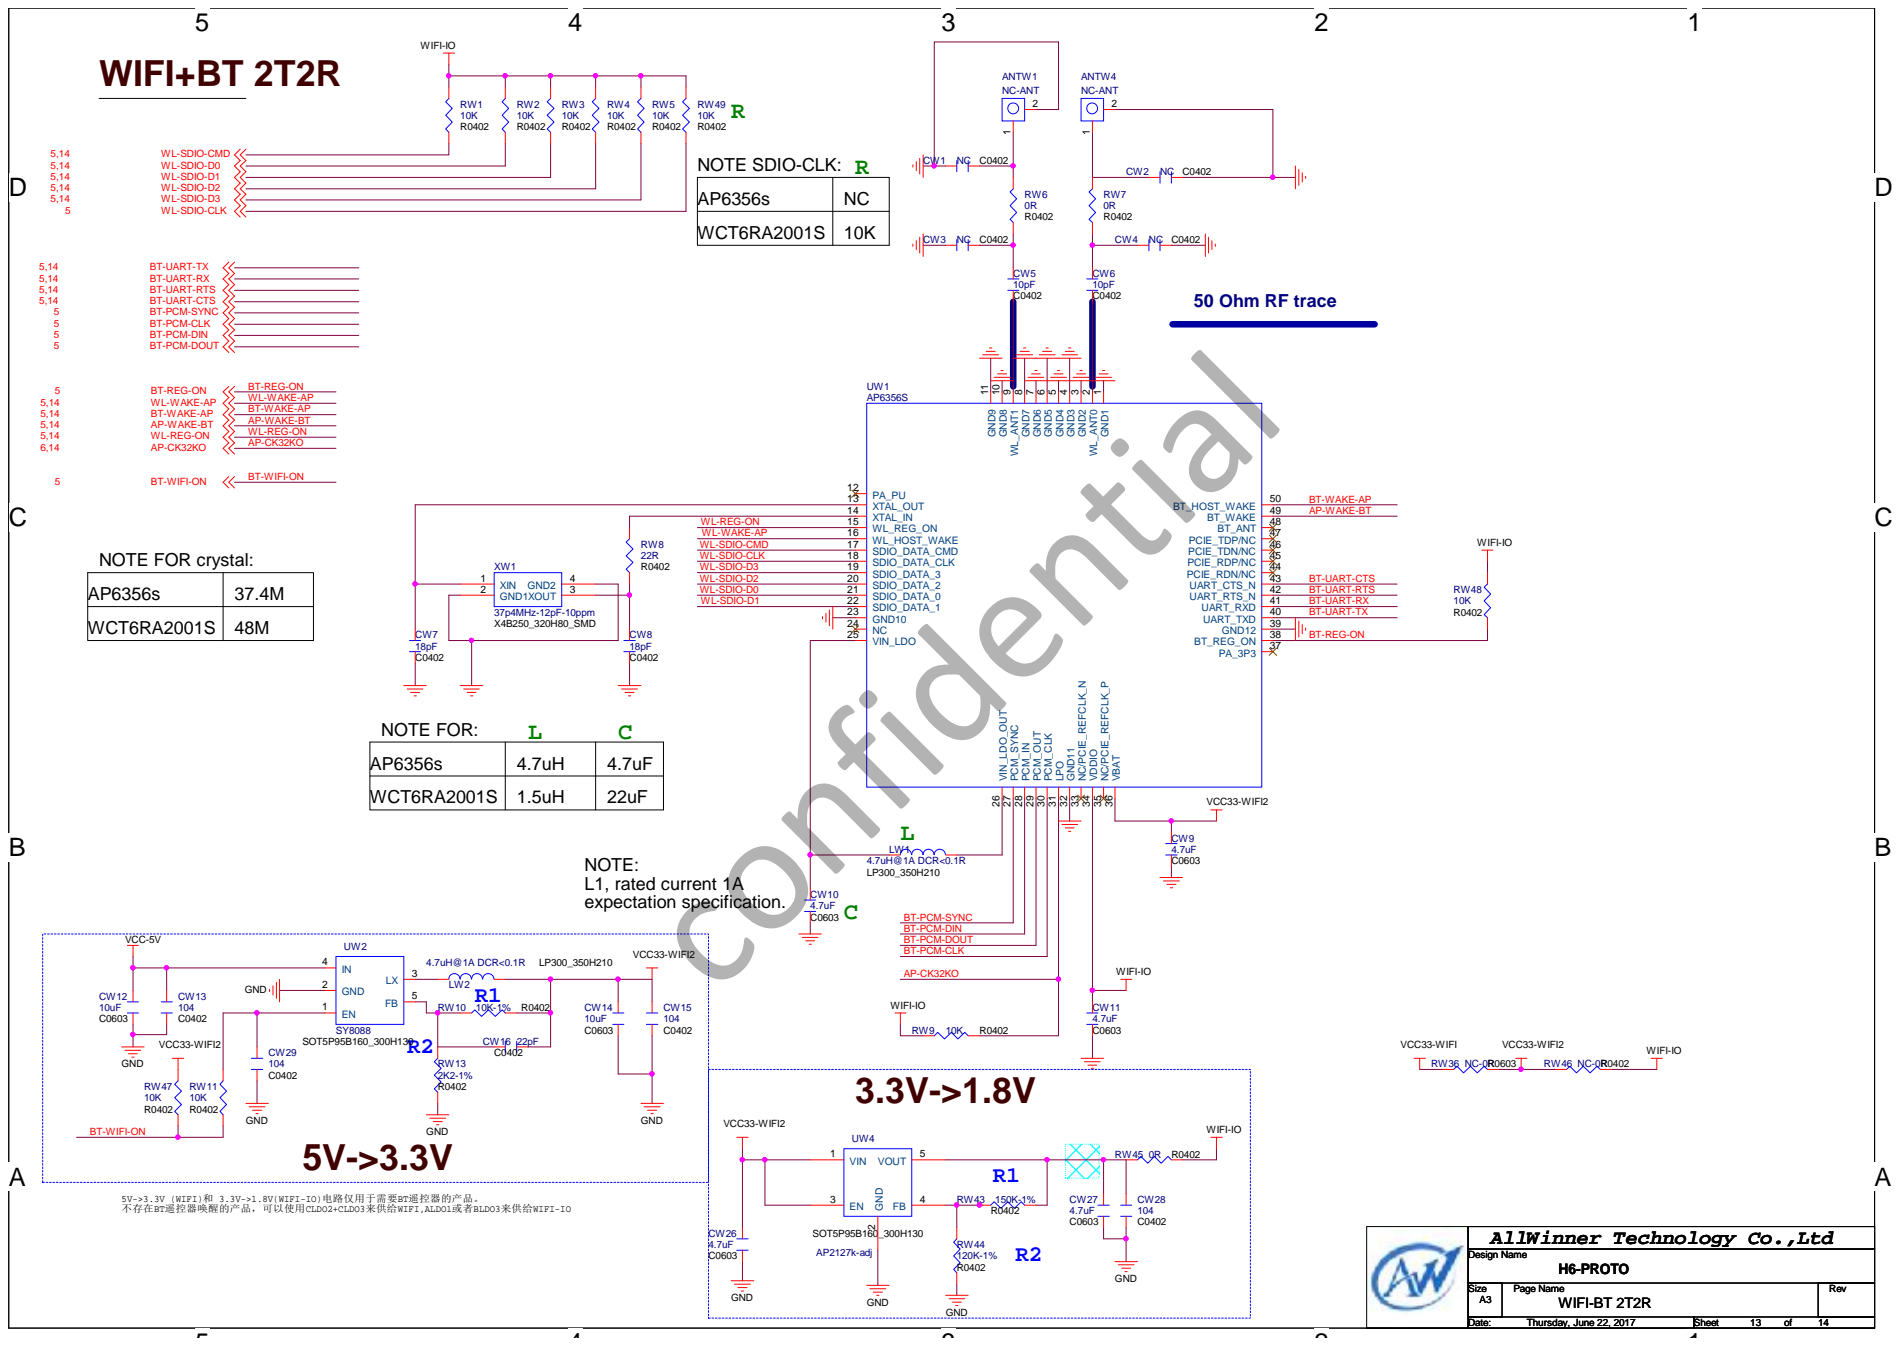
[picture p36: page 13]
NOTE: L1, rated current 1A expectation specification.; NOTE FOR:; WCT6RA2001S; NOTE FOR crystal:; NOTE SDIO-CLK:; WIFI-IO; VCC33-WIFI2; VCC-5V; VCC33-WIFI; WIFI-IO VCC33-WIFI2; GND; GND GND; AP-WAKE-BT; BT-WAKE-AP; WL-WAKE-AP; BT-REG-ON; WL-REG-ON; WL-SDIO-CLK; WL-SDIO-D2; WL-SDIO-D0; WL-SDIO-CMD; WL-SDIO-D1; WL-SDIO-D3; BT-UART-RX; BT-UART-TX; BT-UART-RTS; BT-UART-CTS; BT-PCM-CLK; BT-PCM-SYNC; BT-PCM-DIN; BT-PCM-DOUT; BT-WIFI-ON; Design Name; WIFI-BT 2T2R; Thursday, June 22, 2017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

50 Ohm RF trace

BT-REG-ON
WL-WAKE-AP
BT-WAKE-AP
AP-WAKE-BT
WL-REG-ON

BT-WIFI-ON

WL-SDIO-CMD
WL-SDIO-CLK
WL-SDIO-D3
WL-SDIO-D2
WL-SDIO-D0
WL-SDIO-D1

BT-UART-CTS
BT-UART-RTS
BT-UART-RX
BT-UART-TX

BT-PCM-SYNC
BT-PCM-DIN
BT-PCM-DOUT
BT-PCM-CLK

5V->3.3V (WIFI)和 3.3V->1.8V(WIFI-IO)电路仅用于需要BT遥控器的产品。
不存在BT遥控器唤醒的产品，可以使用CLDO2+CLDO3来供给WIFI,ALDO1或者BLDO3来供给WIFI-IO

AllWinner Technology Co.,Ltd

D | D

# WIFI+BT 1T1R

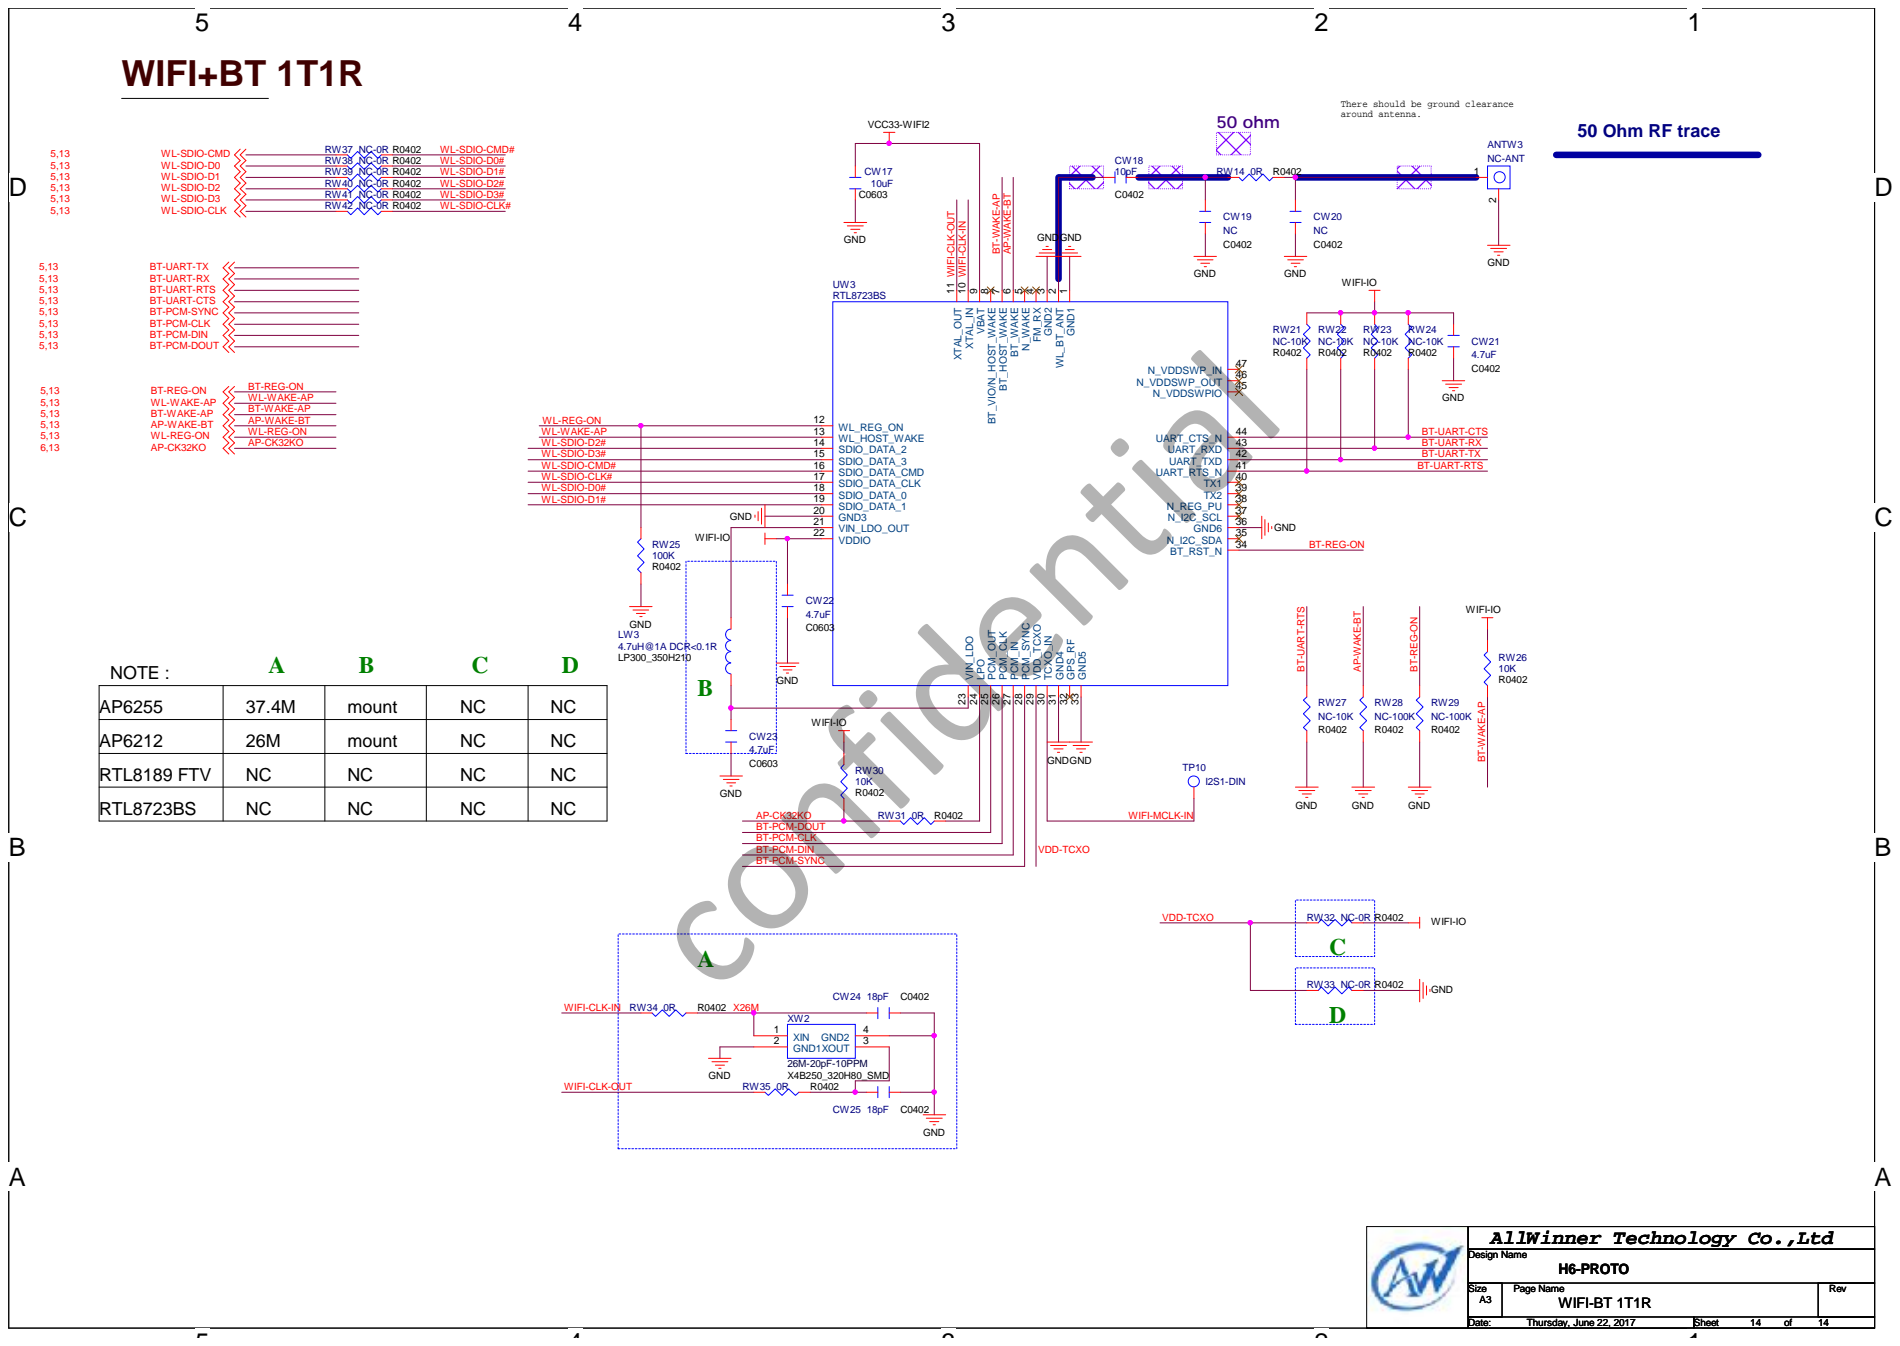
[picture p37: page 14]
around antenna. 50 ohm; 50 Ohm RF trace; NOTE :; VDD-TCXO; WL-SDIO-CMD#; BT-UART-RTS AP⁻WAKE⁻BT; BT-REG-ONAP⁻WAKE⁻BT; WIFI-IO; VCC33-WIFI2; GND; GNDGND; AP-WAKE-BT; BT-WAKE-AP; WL-WAKE-AP; BT-REG-ON; WL-REG-ON; WL-SDIO-CLK; WL-SDIO-D2; WL-SDIO-D0; WL-SDIO-CMD; WL-SDIO-D1; WL-SDIO-D3; BT-UART-RX; BT-UART-TX; BT-UART-RTS; BT-UART-CTS; BT-PCM-CLK; BT-PCM-SYNC; BT-PCM-DIN; BT-PCM-DOUT; Design Name; WIFI-BT 1T1R; Thursday, June 22, 2017; 26M-20pF-10PPM X4B250_320H80_SMD; XIN; 1 GND1 2 XOUT; GND2 3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

There should be ground clearance

WL-SDIO-CMD#
WL-SDIO-D0#
WL-SDIO-D1#
WL-SDIO-D2#
WL-SDIO-D3#
WL-SDIO-CLK#

BT-WAKE-AP

WIFI-CLK-OUT

WIFI-CLK-IN

BT-REG-ON
WL-WAKE-AP
AP-WAKE-BT
WL-REG-ON

BT-UART-CTS
BT-UART-RX
BT-UART-TX

BT-UART-RTS

AP6255 | 37.4M | mount | NC | NC
AP6212 | 26M | mount | NC | NC
RTL8189 FTV | NC | NC | NC | NC
RTL8723BS | NC | NC | NC | NC

BT-PCM-DOUT
BT-PCM-CLK
BT-PCM-DIN
BT-PCM-SYNC

WIFI-MCLK-IN

AllWinner Technology Co.,Ltd
