Commander-bao/BlueberryPi/2.Docs/Allwinner H6/硬件资料/2、DDR模板/2x16/H6_DDR3_2X16_V1_0.pdf

5

4

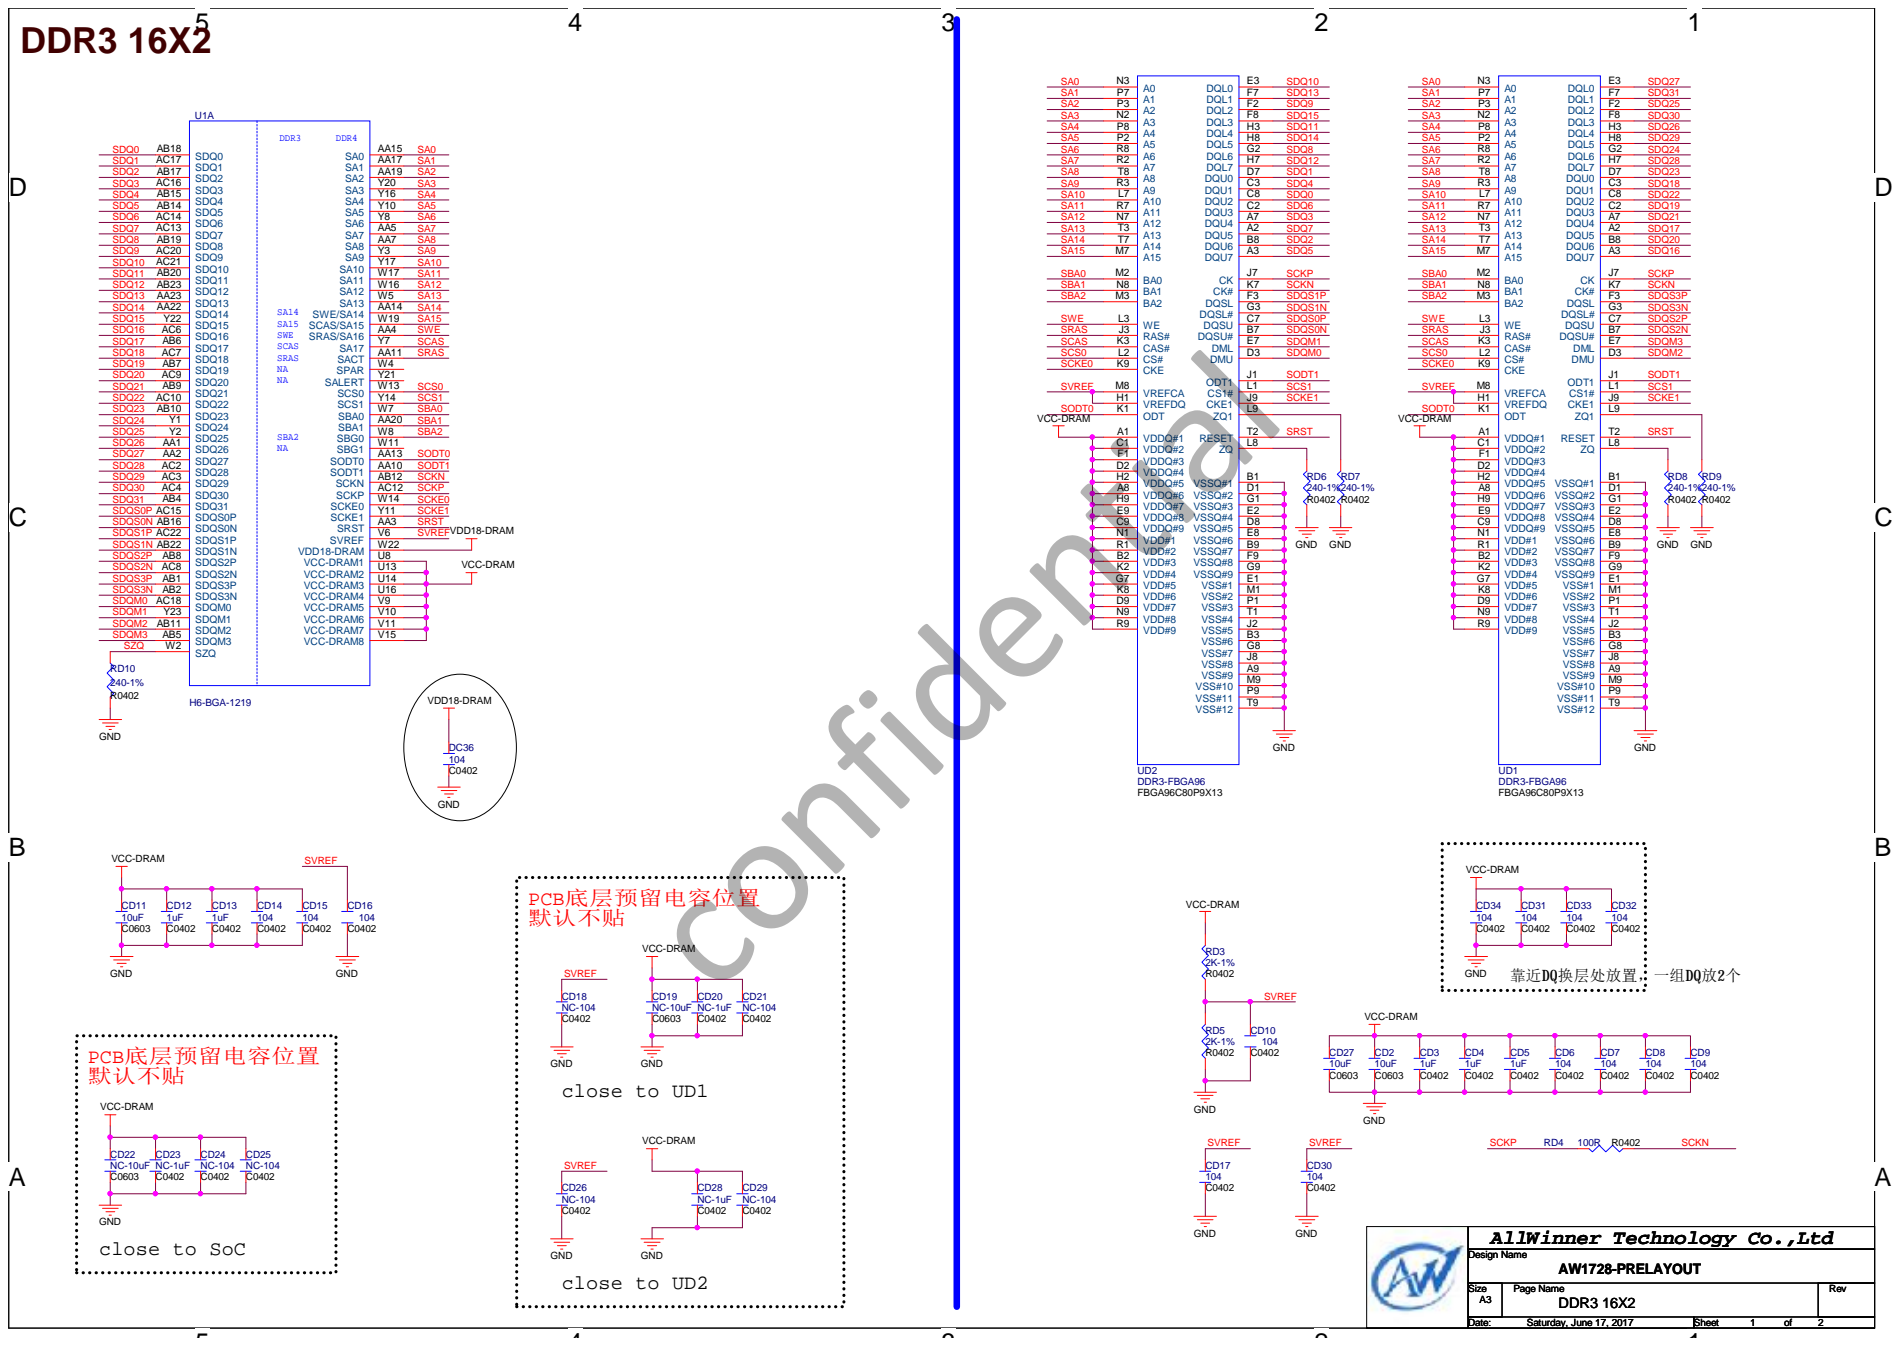
[picture p38: page 1]

AllWinner Technology Co.,Ltd

5

4

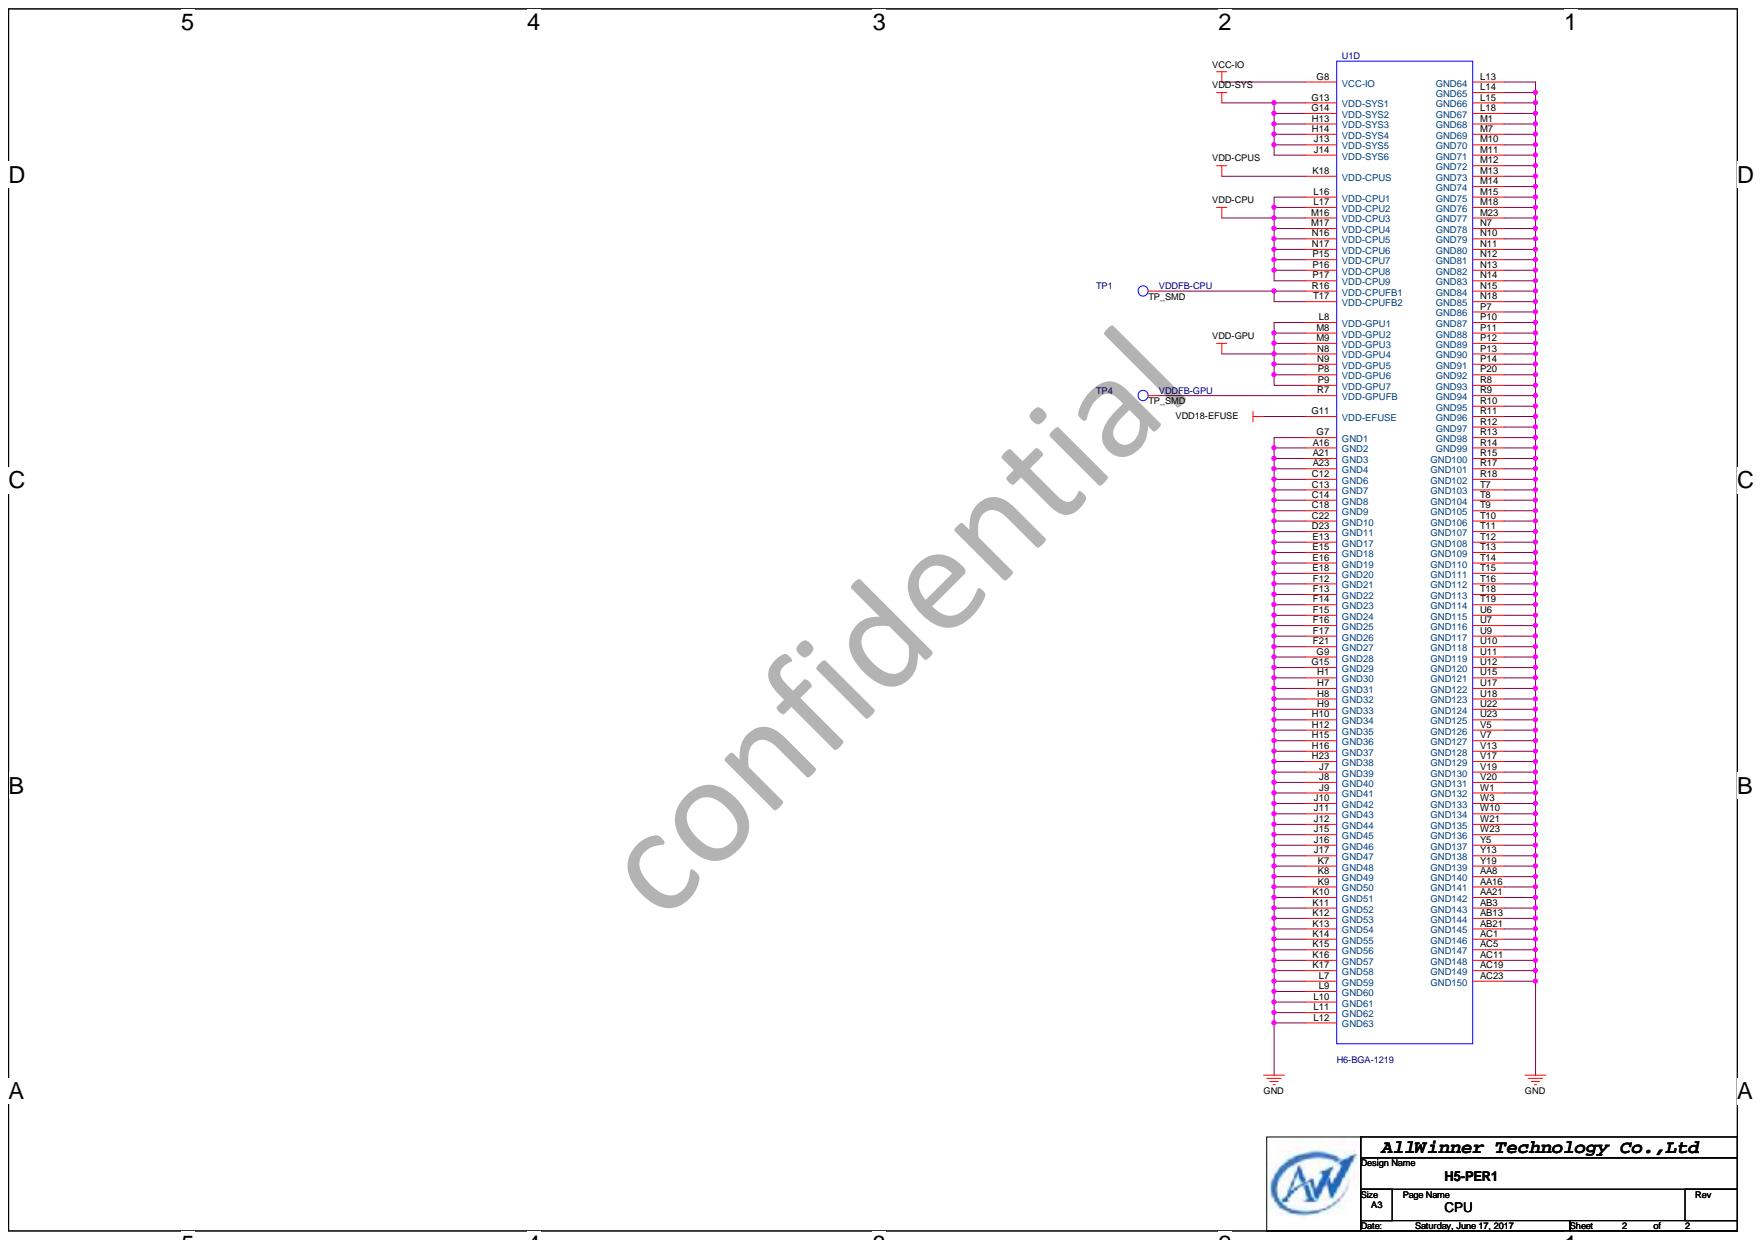
[picture p39: page 2]

AllWinner Technology Co.,Ltd CPU
