Commander-bao/BlueberryPi/2.Docs/Allwinner H6/硬件资料/2、DDR模板/4x16/H6_REF_DDR3_16X4D_V1_0.pdf

# DDR3_16X4D

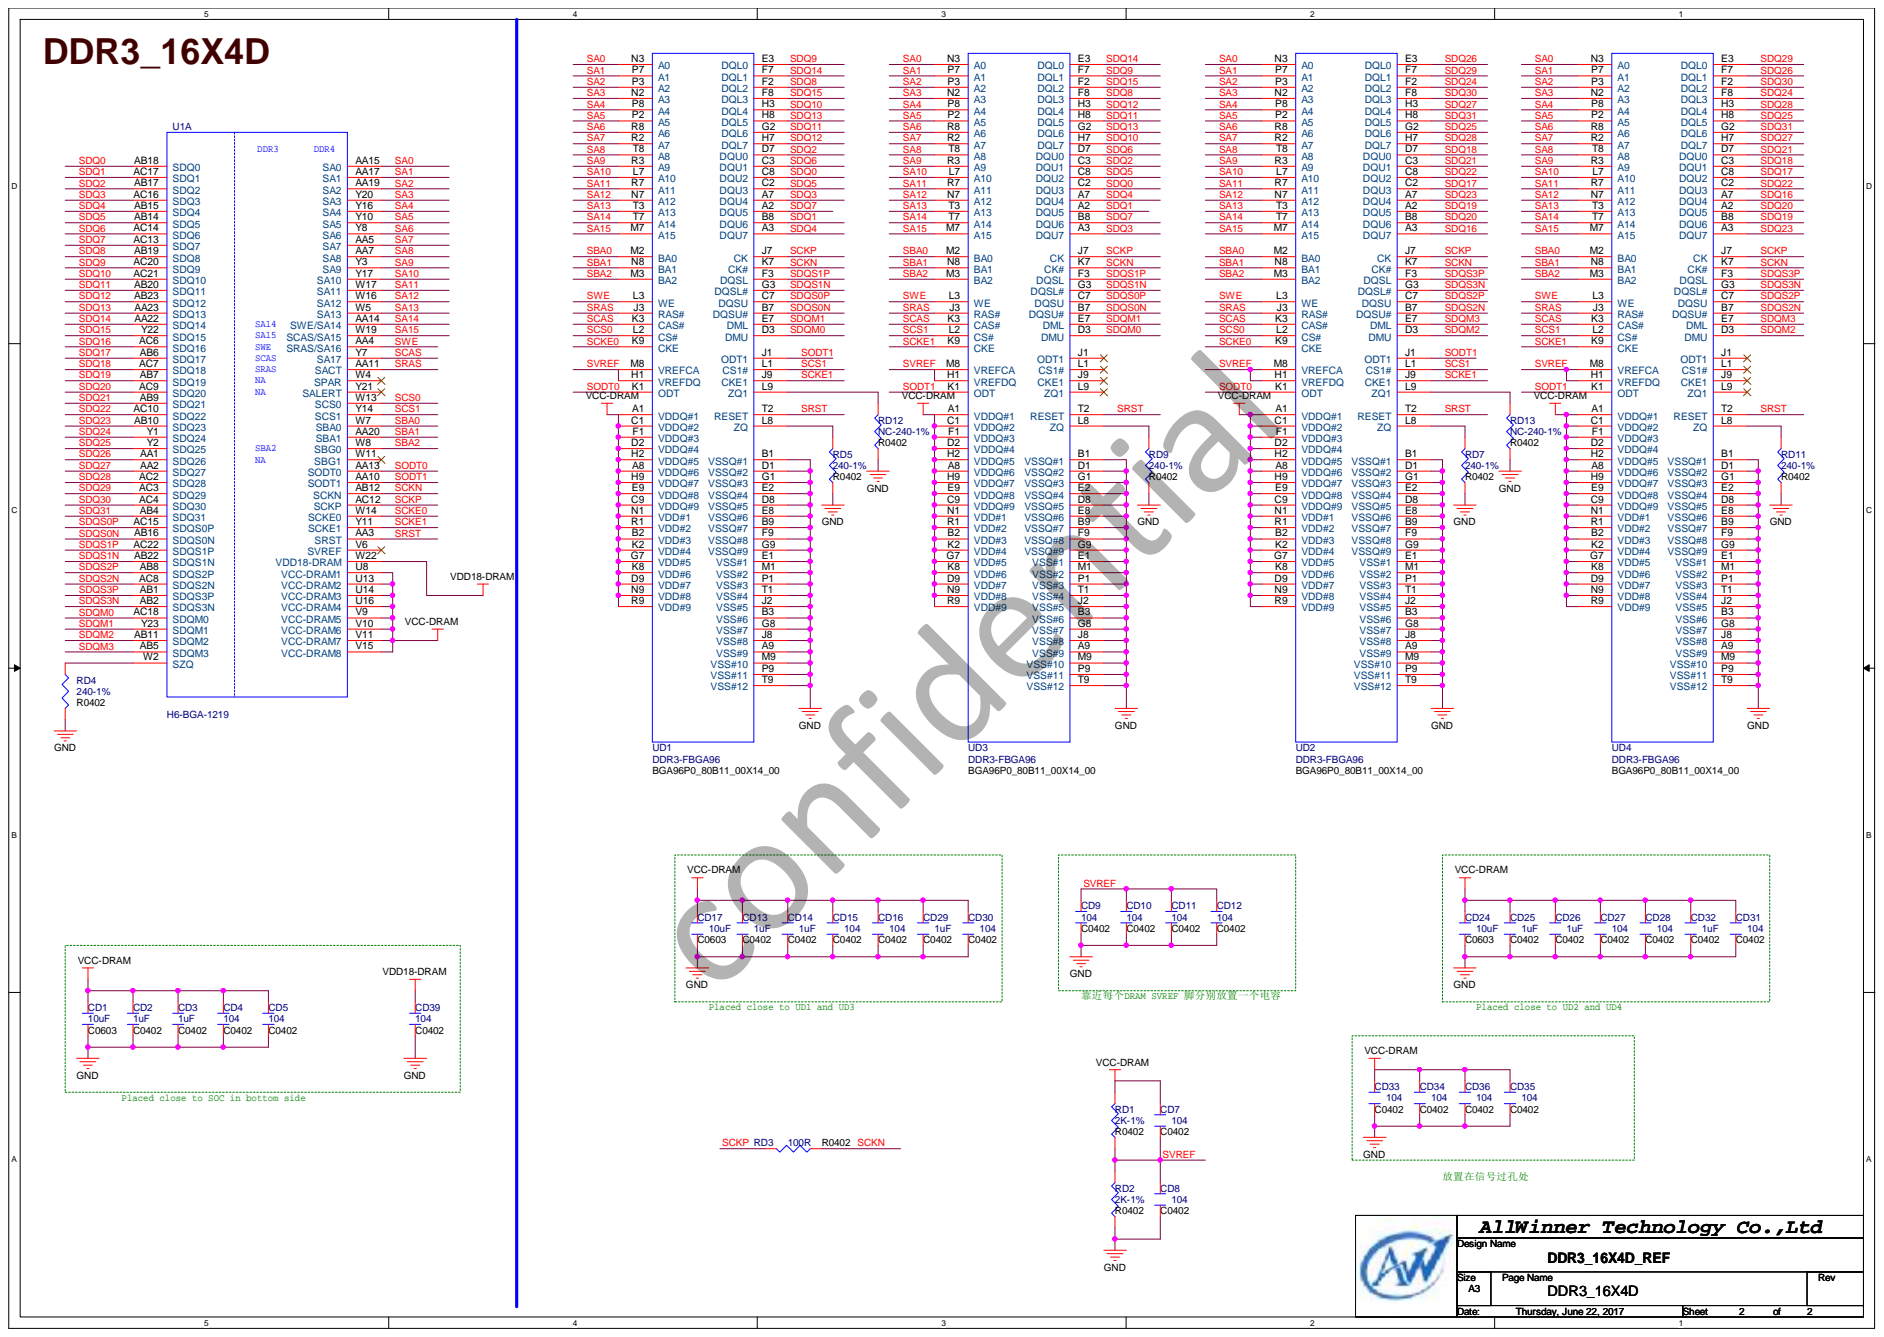
[picture p40: page 1]

Placed close to SOC in bottom side

AllWinner Technology Co.,Ltd
