Commander-bao/BlueberryPi/2.Docs/Allwinner H6/硬件资料/2、DDR模板/DDR4/H6_REF_DDR4_V1_0.pdf

5

4

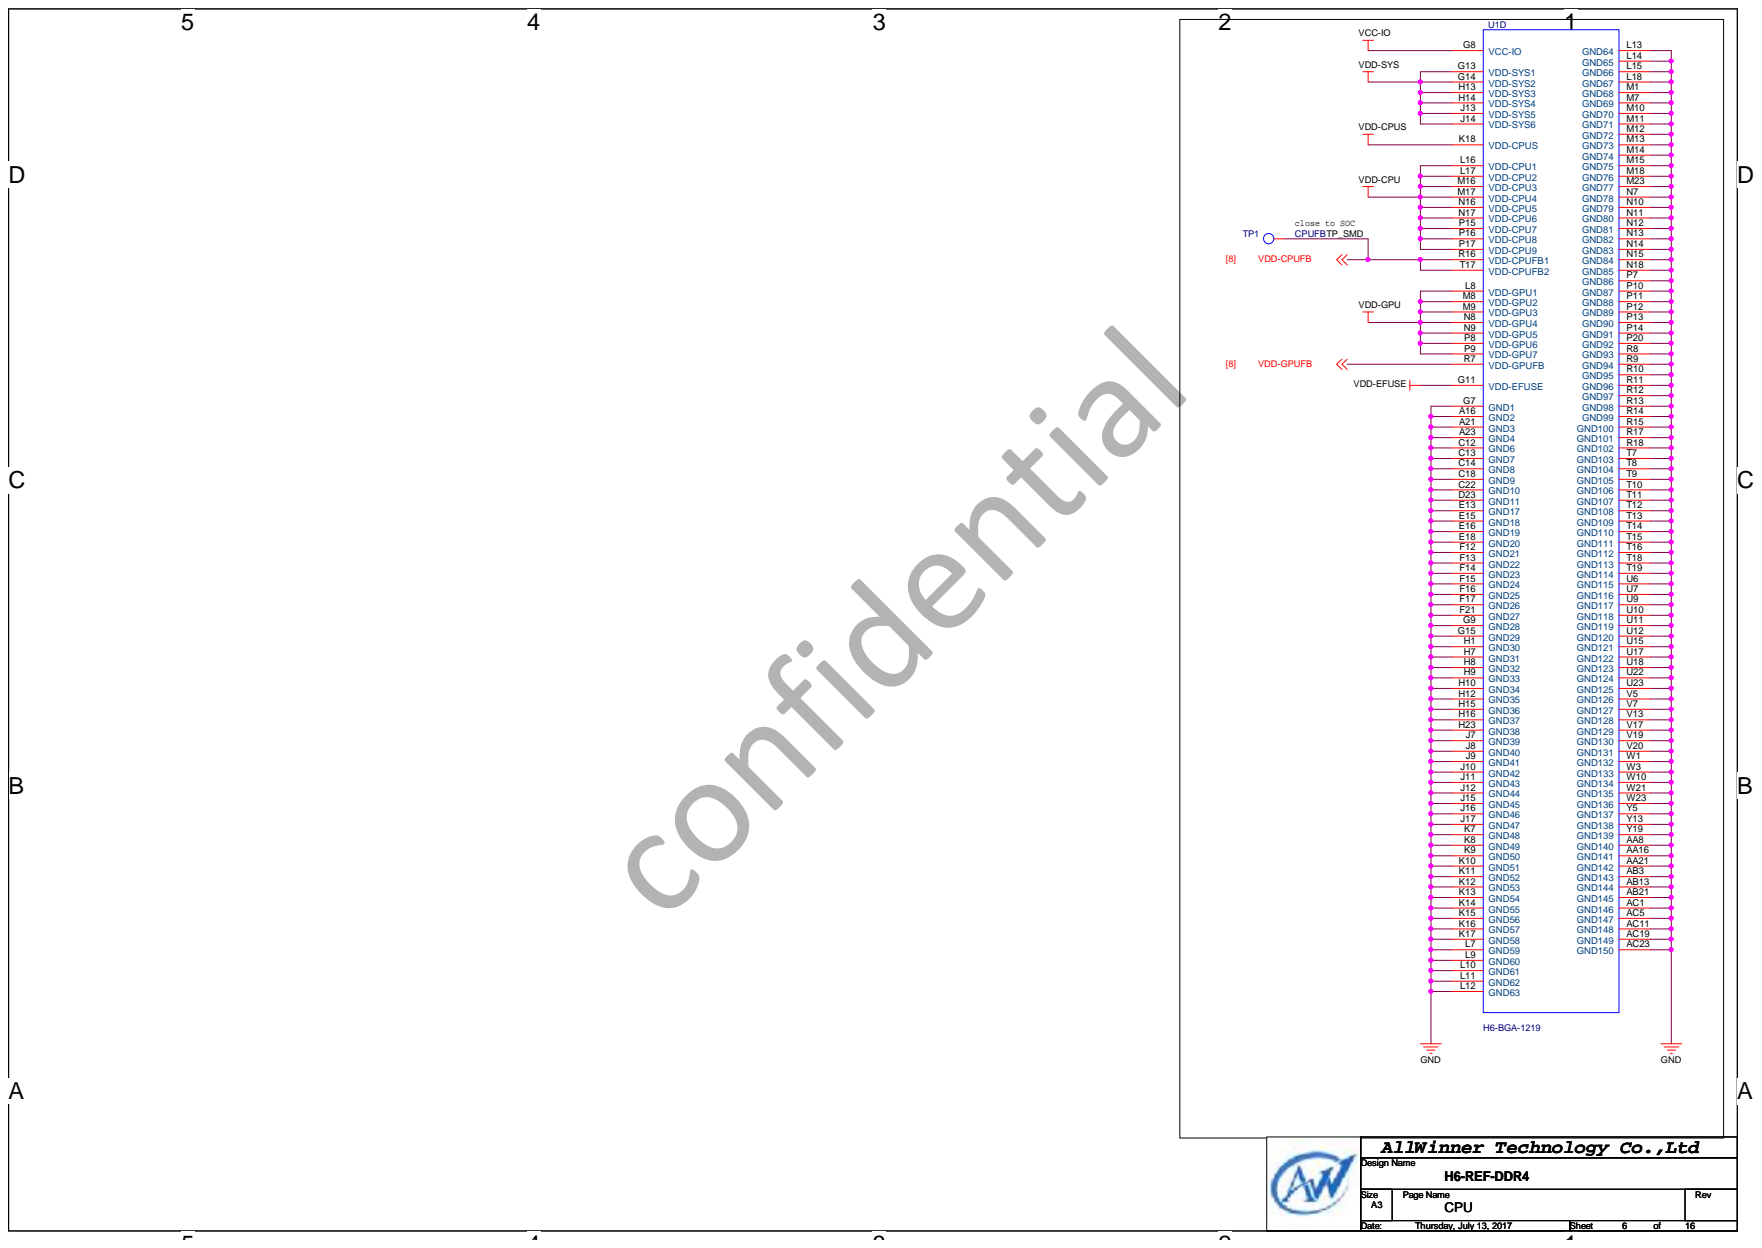
[picture p41: page 1]

AllWinner Technology Co.,Ltd CPU

5

4

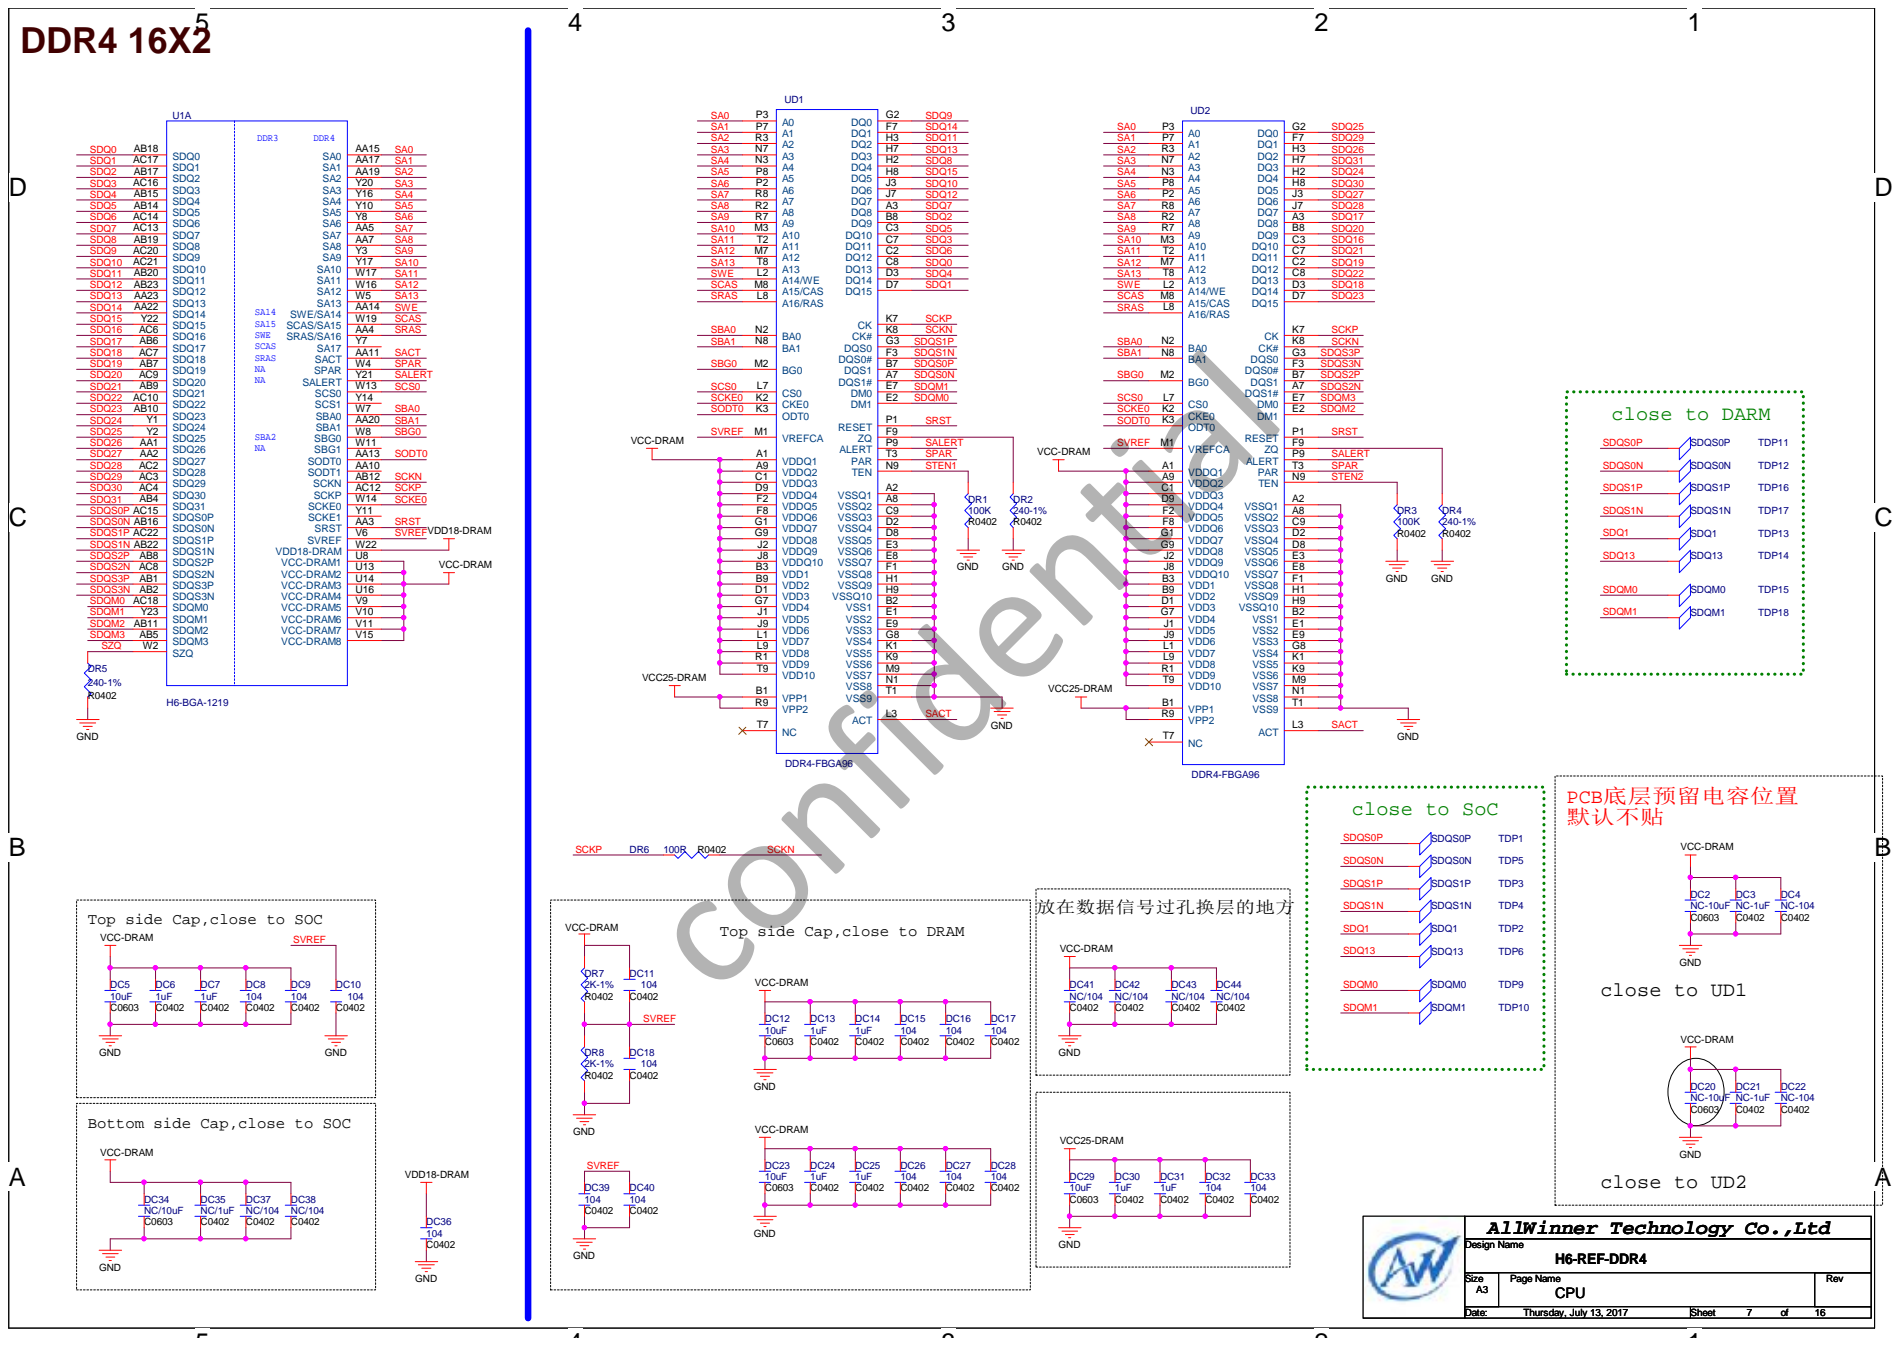
[picture p42: page 2]

Top side Cap,close to SOC

Top side Cap,close to DRAM

Bottom side Cap,close to SOC

AllWinner Technology Co.,Ltd
